tomaskovacik/vwcdavr/dumps/dump_cdc_real_changer_real_radio_audi_concert1.txt

0 CF FF FF 5A 5F FF FF                  CD: 70 track: 0   min: 0 sek: A5
FF FF C7 DE 5A 17 0 7F                  CD: 40 track: 38   min: 21 sek: A5
FF FF FF DE 5A 5F FF FF                  CD: 40 track: 0   min: 21 sek: A5
FF FB 42 D0 F FF FF BC                  CD: 44 track: BD   min: 2F sek: F0
FF FF BC B4 BF FF FF FF                  CD: 40 track: 43   min: 4B sek: 40
B4 FF FF FF FF FF 8F BC                  CD: 40 track: 0   min: 0 sek: 0
FF FF FF FF 8F BC B4 2B                  CD: 40 track: 0   min: 0 sek: 70
B4 BF FF FF B4 FF FF BC                  CD: 0 track: 0   min: 0 sek: 4B
B4 2A 0 FF FF FF FF BC                  CD: 95 track: FF   min: 0 sek: 0
B4 29 0 FF FF FF FF BF                  CD: 96 track: FF   min: 0 sek: 0
532C10EF - DISABLE
B4 BF FF FF FF FF 8F BC                  CD: 0 track: 0   min: 0 sek: 0
532C14EB - end cmd/next cd
D4 7F FF FF FF FF 1F B8                  CD: C0 track: 0   min: 0 sek: 0
7A 5F FF FF FF FF C7 FE                  CD: E0 track: 0   min: 0 sek: 0
F4 29 0 FF FF FF FF F4                  CD: 96 track: FF   min: 0 sek: 0
F4 FF FC FF FF FF FF FC                  CD: 40 track: 3   min: 0 sek: 0
29 0 FF FF FF FF FC F4                  CD: BF track: 0   min: 0 sek: 0
F4 BF FF FF FC FF 8F FC                  CD: 0 track: 0   min: 0 sek: 3
F4 DF FF FF FF FF C7 FE                  CD: 60 track: 0   min: 0 sek: 0
F4 BF FF FF FF FF 8F FC                  CD: 0 track: 0   min: 0 sek: 0
F4 BF FF FF FF FF 8F FE                  CD: 0 track: 0   min: 0 sek: 0
F4 BF FF FF FF FF 8F FC                  CD: 0 track: 0   min: 0 sek: 0
B4 2E 0 FF FF FF FF BC                  CD: 91 track: FF   min: 0 sek: 0
B4 BE FE FF FF FF 6F BC                  CD: 1 track: 1   min: 0 sek: 0
B4 2D 0 FF FF FF FF BC                  CD: 92 track: FF   min: 0 sek: 0
B4 BE FE FF FF FF 6F BC                  CD: 1 track: 1   min: 0 sek: 0
B4 2C 0 FF FF FF FF BC                  CD: 93 track: FF   min: 0 sek: 0
B4 7D FF B4 FF FF FF BC                  CD: C2 track: 0   min: 4B sek: 0
B4 2B 0 FF FF FF FF BC                  CD: 94 track: FF   min: 0 sek: 0
B4 2A 0 FF FF FB FE FF                  CD: 95 track: FF   min: 0 sek: 0
68 7D FD FF FF FE DF 78                  CD: C2 track: 2   min: 0 sek: 0
2D 2F BF BF FF FF DB EF                  CD: 90 track: 40   min: 40 sek: 0
B4 FF FF F7 FF FF 6F BC                  CD: 40 track: 0   min: 8 sek: 0
BE FE FF FF FF 6F BC B4                  CD: 41 track: 0   min: 0 sek: 0
B4 BE FE FF BC 0 FF BC                  CD: 1 track: 1   min: 0 sek: 43
B4 2C 0 FF FF FF FF BC                  CD: 93 track: FF   min: 0 sek: 0
B4 2B 0 FF FF FF FF B4                  CD: 94 track: FF   min: 0 sek: 0
B4 FF 79 FF FF FF FF 7C                  CD: 40 track: 86   min: 0 sek: 0
FF FF FF FF BE 5A 5F 7F                  CD: 40 track: 0   min: 0 sek: 41
B4 29 0 FF BC FF 6F BC                  CD: 96 track: FF   min: 0 sek: 43
B4 BE FE FF FF FF 6F BC                  CD: 1 track: 1   min: 0 sek: 0
B4 2D 0 FF FF FF FF BC                  CD: 92 track: FF   min: 0 sek: 0
B4 BE FE FF FF FF 6F BC                  CD: 1 track: 1   min: 0 sek: 0
B4 2C 0 FF FF FF FF BC                  CD: 93 track: FF   min: 0 sek: 0
B4 BE FF 6F 0 FF FF BC                  CD: 1 track: 0   min: 90 sek: FF
B4 2B 0 FF FF FF FF BC                  CD: 94 track: FF   min: 0 sek: 0
B4 2A 0 FF FF FF B4 FF                  CD: 95 track: FF   min: 0 sek: 0
B4 FF FF FF 6F BC FF BC                  CD: 40 track: 0   min: 0 sek: 90
FF BC B4 BE FE FF FF FF                  CD: 3 track: 4B   min: 41 sek: 1
B4 0 FF B4 FF FF 6F BC                  CD: BF track: 0   min: 4B sek: 0
B4 BE FE FF FF FF 6F BC                  CD: 1 track: 1   min: 0 sek: 0
B4 2C 0 FF FF FF FF BC                  CD: 93 track: FF   min: 0 sek: 0
B4 BE FE FF FF FF 6F BC                  CD: 1 track: 1   min: 0 sek: 0
B4 2B 0 FF FF FF FF BC                  CD: 94 track: FF   min: 0 sek: 0
B4 FF 6F A8 FF FF FF BC                  CD: 40 track: 90   min: 57 sek: 0
B4 2A 0 FF FF FF FF BC                  CD: 95 track: FF   min: 0 sek: 0
B4 29 0 FF FE BE FF BC                  CD: 96 track: FF   min: 0 sek: 1
B4 BE FE FF FF FF 6F BC                  CD: 1 track: 1   min: 0 sek: 0
B4 2D 0 FF FF FF FF BC                  CD: 92 track: FF   min: 0 sek: 0
B4 BE FE FF FF FF 6F BC                  CD: 1 track: 1   min: 0 sek: 0
B4 2C 0 FF FF FF FF BC                  CD: 93 track: FF   min: 0 sek: 0
B4 BE FE FF 6F 2B FF BC                  CD: 1 track: 1   min: 0 sek: 90
B4 2B 0 FF FF FF FF BC                  CD: 94 track: FF   min: 0 sek: 0
B4 2A 0 FF FF FF FF BC                  CD: 95 track: FF   min: 0 sek: 0
B4 FE 6F FF FF FF FF BC                  CD: 41 track: 90   min: 0 sek: 0
FF FF FF FF BC B4 BE FE                  CD: 40 track: 0   min: 0 sek: 43
B4 2E 0 FF 74 FF B7 DE                  CD: 91 track: FF   min: 0 sek: 8B
BA 5F 7F 7F FF FF B7 DE                  CD: E0 track: 80   min: 80 sek: 0
B4 BE FE FF FF BC FF FF                  CD: 1 track: 1   min: 0 sek: 0
B4 FF FF FF FF BC 6F BC                  CD: 40 track: 0   min: 0 sek: 0
6F BC B4 2B 0 FF FF FF                  CD: 3 track: 4B   min: D4 sek: FF
B4 FF 6F 2A FF FF FF BC                  CD: 40 track: 90   min: D5 sek: 0
B4 2A 0 FF FF FF FF BC                  CD: 95 track: FF   min: 0 sek: 0
B4 29 0 FF FF FE FF BC                  CD: 96 track: FF   min: 0 sek: 0
B4 BE FE FF FF FF 6F BC                  CD: 1 track: 1   min: 0 sek: 0
B4 2D 0 FF FF FF FF BC                  CD: 92 track: FF   min: 0 sek: 0
B4 BD FE FF FF FF 6F BC                  CD: 2 track: 1   min: 0 sek: 0
B4 2C 0 FF FF FF FF BC                  CD: 93 track: FF   min: 0 sek: 0
B4 BD FE FF B4 0 FF BC                  CD: 2 track: 1   min: 0 sek: 4B
B4 2B 0 FF FF FF FF BC                  CD: 94 track: FF   min: 0 sek: 0
B4 2A 0 FF FF FF FF BC                  CD: 95 track: FF   min: 0 sek: 0
B4 FF 6F FF FF FF FF BC                  CD: 40 track: 90   min: 0 sek: 0
0 FF FF FF FF BC B4 BD                  CD: 40 track: 0   min: 0 sek: 0
B4 2E EC DC B4 FF 6F BC                  CD: 91 track: 13   min: 23 sek: 4B
B4 BD FE FF FF FF 6F BC                  CD: 2 track: 1   min: 0 sek: 0
B4 2C 0 FF FF FF FF BC                  CD: 93 track: FF   min: 0 sek: 0
B4 BD FE FF FF FF 6F BC                  CD: 2 track: 1   min: 0 sek: 0
B4 2B 0 FF FF FF FF BC                  CD: 94 track: FF   min: 0 sek: 0
9A 5E FF DE 2A FF FF BC                  CD: E1 track: 0   min: 21 sek: D5
B4 2A 0 FF FF FF FF BC                  CD: 95 track: FF   min: 0 sek: 0
B4 29 0 FF FF FF FE FF                  CD: 96 track: FF   min: 0 sek: 0
B4 FF FF FF 6F BC FF BC                  CD: 40 track: 0   min: 0 sek: 90
FF BC B4 BD FE FF FF FF                  CD: 3 track: 4B   min: 42 sek: 1
B4 FF FF FE FF FF 6F BC                  CD: 40 track: 0   min: 1 sek: 0
B4 BD FE FF FF FF 6F BC                  CD: 2 track: 1   min: 0 sek: 0
B4 2B 0 FF FF FF FF BC                  CD: 94 track: FF   min: 0 sek: 0
B4 BD FE FF FF FF 6F BC                  CD: 2 track: 1   min: 0 sek: 0
B4 2A 0 FF FF FF FF BC                  CD: 95 track: FF   min: 0 sek: 0
B4 FF 6F 0 FF FF FF BC                  CD: 40 track: 90   min: FF sek: 0
29 0 FF FF FF FF BC B4                  CD: BF track: 0   min: 0 sek: 0
B4 2E EC CE FF FE FF BC                  CD: 91 track: 13   min: 31 sek: 0
B4 BD FE FF FF FF 6F BC                  CD: 2 track: 1   min: 0 sek: 0
B4 2C 0 FF FF FF FF BC                  CD: 93 track: FF   min: 0 sek: 0
B4 BD FE FF FF FF 6F BC                  CD: 2 track: 1   min: 0 sek: 0
B4 2B 0 FF FF FF FF DE                  CD: 94 track: FF   min: 0 sek: 0
B4 BD FE B7 2A FF FF BC                  CD: 2 track: 1   min: 48 sek: D5
B4 2A 0 FF FF FF FF BC                  CD: 95 track: FF   min: 0 sek: 0
B4 29 0 7F FF FF DE FF                  CD: 96 track: FF   min: 80 sek: 0
B4 FF FB 7D ED DC FF BC                  CD: 40 track: 4   min: 82 sek: 12
DD CF FB CB 4B CF EF FF                  CD: 70 track: 4   min: 34 sek: B4
B4 FF FF BC FF FF 6F BC                  CD: 40 track: 0   min: 43 sek: 0
B4 BC FE FF FF FF 6F BC                  CD: 3 track: 1   min: 0 sek: 0
B4 2B 80 7F FF FF FF DE                  CD: 94 track: 7F   min: 80 sek: 0
B4 BC FE FF FF FF 6F BC                  CD: 3 track: 1   min: 0 sek: 0
B4 2A 0 FF FF FF FF B4                  CD: 95 track: FF   min: 0 sek: 0
B4 FF 6F BC FF FF FF BC                  CD: 40 track: 90   min: 43 sek: 0
FF FF FF BC B4 BC FE FF                  CD: 40 track: 0   min: 43 sek: 4B
B4 67 FF BC FF FF 6F BC                  CD: D8 track: 0   min: 43 sek: 0
B4 BC FE FF FF FF 6F BC                  CD: 3 track: 1   min: 0 sek: 0
B4 2C 0 FF FF FF FF BC                  CD: 93 track: FF   min: 0 sek: 0
B4 BC FE FF FF FF 6F BC                  CD: 3 track: 1   min: 0 sek: 0
B4 2B 0 7F FF FF FF DE                  CD: 94 track: FF   min: 80 sek: 0
B4 FF DF A8 FF FF FF EF                  CD: 40 track: 20   min: 57 sek: 0
B4 2A 0 7F FF FF FF EF                  CD: 95 track: FF   min: 80 sek: 0
B4 29 0 FF BC FE FF BC                  CD: 96 track: FF   min: 0 sek: 43
B4 BC FE FF FF FF 6F BC                  CD: 3 track: 1   min: 0 sek: 0
B4 DA 0 FF FF FF FF BC                  CD: 65 track: FF   min: 0 sek: 0
5A BC FE FF FF FF 6F BC                  CD: 3 track: 1   min: 0 sek: 0
5A B 0 3F FF FF FF F7                  CD: B4 track: FF   min: C0 sek: 0
B4 BC FE FF 15 FF FF BC                  CD: 3 track: 1   min: 0 sek: EA
B4 2B 0 FF FF FF FF BC                  CD: 94 track: FF   min: 0 sek: 0
B4 2A 0 FF FF FF FF BC                  CD: 95 track: FF   min: 0 sek: 0
B4 FF DE FF FF FF FF BC                  CD: 40 track: 21   min: 0 sek: 0
FF FF FF FF BC B4 BC FE                  CD: 40 track: 0   min: 0 sek: 43
B4 CE FF BC FF FF 6F BC                  CD: 71 track: 0   min: 43 sek: 0
B4 BC FE FF FF FF 6F BC                  CD: 3 track: 1   min: 0 sek: 0
B4 2C 0 FF FF FF FF BC                  CD: 93 track: FF   min: 0 sek: 0
B4 BC FE FF FF FF 6F BC                  CD: 3 track: 1   min: 0 sek: 0
B4 2B 0 FF FF FF FF BC                  CD: 94 track: FF   min: 0 sek: 0
B4 FF 6F 1 FF FF FF DE                  CD: 40 track: 90   min: FE sek: 0
B4 2A 0 FF FF FF FF DE                  CD: 95 track: FF   min: 0 sek: 0
B4 29 0 FF FF BC FF 6F                  CD: 96 track: FF   min: 0 sek: 0
B4 BC FE FF FF FF 6F BC                  CD: 3 track: 1   min: 0 sek: 0
B4 6D 0 FF FF FF FF DE                  CD: D2 track: FF   min: 0 sek: 0
B4 BC FE FF FF FF 6F BC                  CD: 3 track: 1   min: 0 sek: 0
B4 2C 0 FF FF FF FF BC                  CD: 93 track: FF   min: 0 sek: 0
B4 BC FE FF 6F 2B FF BC                  CD: 3 track: 1   min: 0 sek: 90
B4 2B 0 FF FF FF FF BC                  CD: 94 track: FF   min: 0 sek: 0
B4 2A 0 FF FF FF FF BC                  CD: 95 track: FF   min: 0 sek: 0
B4 FE 6F FF FF FF FF BC                  CD: 41 track: 90   min: 0 sek: 0
0 FF FF FF FF BC B4 BC                  CD: 40 track: 0   min: 0 sek: 0
B4 2E EC CE FF BC FF BC                  CD: 91 track: 13   min: 31 sek: 0
B4 BC FE FF FF FF 6F BC                  CD: 3 track: 1   min: 0 sek: 0
B4 2C 0 FF FF FF FF BC                  CD: 93 track: FF   min: 0 sek: 0
B4 BC FE FF FF FF 6F BC                  CD: 3 track: 1   min: 0 sek: 0
B4 2B 0 FF FF FF FF BC                  CD: 94 track: FF   min: 0 sek: 0
B4 BC FE 6F 2A FF FF BC                  CD: 3 track: 1   min: 90 sek: D5
B4 2A 0 FF FF FF FF BC                  CD: 95 track: FF   min: 0 sek: 0
B4 29 0 FF FF FF FF FE                  CD: 96 track: FF   min: 0 sek: 0
B4 FF 6F BC AD DC FF BC                  CD: 40 track: 90   min: 43 sek: 52
AD DC FF BC B4 BC FE FF                  CD: 63 track: 0   min: 43 sek: 4B
B4 FF FF FE FF FF 6F BC                  CD: 40 track: 0   min: 1 sek: 0
BC FE FF FF FF 6F BC B4                  CD: 41 track: 0   min: 0 sek: 0
B4 BC FE FF 6F 0 FF BC                  CD: 3 track: 1   min: 0 sek: 90
B4 2B 0 FF FF FF FF BC                  CD: 94 track: FF   min: 0 sek: 0
B4 2A 0 FF FF FF FF B4                  CD: 95 track: FF   min: 0 sek: 0
B4 FF 6F FF FF FF FF BC                  CD: 40 track: 90   min: 0 sek: 0
29 0 FF FF FF FF BC B4                  CD: BF track: 0   min: 0 sek: 0
B4 2E EC CE FF BC FF DE                  CD: 91 track: 13   min: 31 sek: 0
B4 BC FE FF FF FF 6F DE                  CD: 3 track: 1   min: 0 sek: 0
B4 BC FE FF FF FF F7 2C                  CD: 3 track: 1   min: 0 sek: 0
B4 FF FF FF FF FF 6F BC                  CD: 40 track: 0   min: 0 sek: 0
FF FF FF 6F BC B4 2B 0                  CD: 40 track: 0   min: 90 sek: 43
B4 BC FF 6F 0 FF FF BC                  CD: 3 track: 0   min: 90 sek: FF
B4 2A 0 FF FF FF FF BC                  CD: 95 track: FF   min: 0 sek: 0
B4 29 0 FF FF FF B4 FE                  CD: 96 track: FF   min: 0 sek: 0
B4 FF EE FB CD DC FF BC                  CD: 40 track: 11   min: 4 sek: 32
6E E7 FD E5 A5 E7 F7 FF                  CD: 58 track: 2   min: 1A sek: 5A
B4 FF BC FE FF FF 6F BC                  CD: 40 track: 43   min: 1 sek: 0
BC FE FF FF FF 6F BC B4                  CD: 41 track: 0   min: 0 sek: 0
B4 BC 7F FF DE FF FF BC                  CD: 3 track: 80   min: 0 sek: 21
B4 2B 0 FF FF FF FF BC                  CD: 94 track: FF   min: 0 sek: 0
B4 2A 0 FF FF FF FF B4                  CD: 95 track: FF   min: 0 sek: 0
B4 FE 6F BC FF FF FF BC                  CD: 41 track: 90   min: 43 sek: 0
FF FF FF BC B4 BB FE FF                  CD: 40 track: 0   min: 43 sek: 4B
B4 EC AD B4 FF FF 6F BC                  CD: 53 track: 52   min: 4B sek: 0
B4 BB FE FF FF FF 6F BC                  CD: 4 track: 1   min: 0 sek: 0
B4 BB FE FF 6F 2C 8E BC                  CD: 4 track: 1   min: 0 sek: 90
B4 2C E8 8E 98 CE FF BC                  CD: 93 track: 17   min: 71 sek: 67
B4 2B 0 FF FF FF FF FF                  CD: 94 track: FF   min: 0 sek: 0
B4 FF BC FF FF FF FF BC                  CD: 40 track: 43   min: 0 sek: 0
FF FF FF FF BC B4 BB FE                  CD: 40 track: 0   min: 0 sek: 43
B4 29 FF EF 77 FF B7 DE                  CD: 96 track: 0   min: 10 sek: 88
B4 BB FF 7F FF FF B7 DE                  CD: 4 track: 0   min: 80 sek: 0
B4 BB FE FF ED C1 FF EF                  CD: 4 track: 1   min: 0 sek: 12
B0 6D 0 FF FF FF FF BC                  CD: D2 track: FF   min: 0 sek: 0
B4 2C E8 8E 98 CE FF BC                  CD: 93 track: 17   min: 71 sek: 67
B4 FF BE FF FF FF FF BC                  CD: 40 track: 41   min: 0 sek: 0
0 FF FF FF FF BC B4 BB                  CD: 40 track: 0   min: 0 sek: 0
B4 2A 0 FF B4 FF 6F BC                  CD: 95 track: FF   min: 0 sek: 4B
B4 BB FE FF FF FF 6F BC                  CD: 4 track: 1   min: 0 sek: 0
B4 2E EC CE AD DC FF BC                  CD: 91 track: 13   min: 31 sek: 52
B4 BB FE FF FF FF 6F 9E                  CD: 4 track: 1   min: 0 sek: 0
B4 6D 0 FF FF FF FF BC                  CD: D2 track: FF   min: 0 sek: 0
B4 BF FF B4 8E CE FF BC                  CD: 0 track: 0   min: 4B sek: 71
B4 2C E8 8E 98 CE FF BC                  CD: 93 track: 17   min: 71 sek: 67
B4 2B 0 FF BC FF 6F BC                  CD: 94 track: FF   min: 0 sek: 43
B4 BB FE FF FF FF 6F BC                  CD: 4 track: 1   min: 0 sek: 0
5A 5D FF 7F FF FF B7 B4                  CD: E2 track: 0   min: 80 sek: 0
B4 FF FF BC FF FF 6F BC                  CD: 40 track: 0   min: 43 sek: 0
FF FF 6F BC B4 2E EC CE                  CD: 40 track: 90   min: 43 sek: 4B
B4 FE 6F B4 FF FF FF BC                  CD: 41 track: 90   min: 4B sek: 0
B4 6D 0 FF FF FF FF BC                  CD: D2 track: FF   min: 0 sek: 0
B4 2C E8 8E CE BB FF BC                  CD: 93 track: 17   min: 71 sek: 31
B4 BB FE FF FF FF 6F BC                  CD: 4 track: 1   min: 0 sek: 0
B4 2A 0 FF FF FF FF BC                  CD: 95 track: FF   min: 0 sek: 0
B4 BB FE FF FF FF 6F BC                  CD: 4 track: 1   min: 0 sek: 0
B4 29 0 FF FF FF FF DE                  CD: 96 track: FF   min: 0 sek: 0
B6 5D FF FB EC DC 7F DE                  CD: E2 track: 0   min: 4 sek: 13
B4 2E EC CE AD DC 7F DE                  CD: 91 track: 13   min: 31 sek: 52
B4 6D 0 FF FF BC F7 6F                  CD: D2 track: FF   min: 0 sek: 0
B4 BB FE FF FF FF 6F BC                  CD: 4 track: 1   min: 0 sek: 0
B4 BB FE 7F FF FF B7 DE                  CD: 4 track: 1   min: 80 sek: 0
B4 0 FF BB FF FF 6F BC                  CD: BF track: 0   min: 44 sek: 0
B4 BB FE FF FF FF 6F BC                  CD: 4 track: 1   min: 0 sek: 0
B4 29 0 FF FF FF FF BC                  CD: 96 track: FF   min: 0 sek: 0
B4 BB FE FF FF FF 6F BC                  CD: 4 track: 1   min: 0 sek: 0
B4 2E EC CE AD DC FF BC                  CD: 91 track: 13   min: 31 sek: 52
5A 7F B7 0 FF FF FF BC                  CD: C0 track: 48   min: FF sek: 0
6D 0 FF FF FF FF BC B4                  CD: BF track: 0   min: 0 sek: 0
B4 2C E8 98 BC FE 6F BC                  CD: 93 track: 17   min: 67 sek: 43
B4 BB FE FF FF FF 6F BC                  CD: 4 track: 1   min: 0 sek: 0
B4 2A 0 FF FF FF FF BC                  CD: 95 track: FF   min: 0 sek: 0
B4 BB FE FF FF FF 6F BC                  CD: 4 track: 1   min: 0 sek: 0
B4 29 0 FF FF FF FF BC                  CD: 96 track: FF   min: 0 sek: 0
B4 BB FF FF 2E AD FF BC                  CD: 4 track: 0   min: 0 sek: D1
B4 2E EC CE AD DC FF BC                  CD: 91 track: 13   min: 31 sek: 52
B4 6D 0 FF FF BC FE FF                  CD: D2 track: FF   min: 0 sek: 0
B4 FD FF FF FE DF BD 78                  CD: 42 track: 0   min: 0 sek: 1
BC 5A 5D FF 7F FF FF B7                  CD: E5 track: A2   min: 0 sek: 80
B4 FF BC FE FF FF 6F BC                  CD: 40 track: 43   min: 1 sek: 0
B4 BB FE FF FF FF 6F BC                  CD: 4 track: 1   min: 0 sek: 0
B4 29 0 FF FF FF FF BC                  CD: 96 track: FF   min: 0 sek: 0
B4 BB FE FF FF FF 6F BC                  CD: 4 track: 1   min: 0 sek: 0
B4 2E EC CE AD DC FF B4                  CD: 91 track: 13   min: 31 sek: 52
B4 FF 6F BC FF FF FF BC                  CD: 40 track: 90   min: 43 sek: 0
FF FF FF BC B4 BB FE FF                  CD: 40 track: 0   min: 43 sek: 4B
B4 8E CE BB FF FF 6F BC                  CD: 31 track: 31   min: 44 sek: 0
B4 BB FE FF FF FF 6F BC                  CD: 4 track: 1   min: 0 sek: 0
B4 2A 0 FF FF FF FF BC                  CD: 95 track: FF   min: 0 sek: 0
B6 5D FF 7F FF FF B7 DE                  CD: E2 track: 0   min: 80 sek: 0
B4 29 0 FF FF FF FF B4                  CD: 96 track: FF   min: 0 sek: 0
B4 FF DE CE AD DC FF BC                  CD: 40 track: 21   min: 31 sek: 52
D9 9D 5B B9 FF 79 69 77                  CD: 22 track: A4   min: 46 sek: 0
B4 0 FF BC FF FF 6F BC                  CD: BF track: 0   min: 43 sek: 0
B4 BB FE FF FF FF 6F BC                  CD: 4 track: 1   min: 0 sek: 0
B4 2B E6 6E 87 D7 FF BC                  CD: 94 track: 19   min: 91 sek: 78
B4 BB FE FF FF FF 6F BC                  CD: 4 track: 1   min: 0 sek: 0
B4 2A 0 FF FF FF FF BC                  CD: 95 track: FF   min: 0 sek: 0
B4 FE 6F FF FF FF FF BC                  CD: 41 track: 90   min: 0 sek: 0
29 0 FF FF FF FF BC B4                  CD: BF track: 0   min: 0 sek: 0
B4 2E EC D5 BC FE FF BC                  CD: 91 track: 13   min: 2A sek: 43
B4 BB FE FF FF FF 6F BC                  CD: 4 track: 1   min: 0 sek: 0
B4 2C E8 8E 98 CF 7F DE                  CD: 93 track: 17   min: 71 sek: 67
B4 BA FE FF FF FF 6F BC                  CD: 5 track: 1   min: 0 sek: 0
B4 2B E6 6E 87 D7 FF BC                  CD: 94 track: 19   min: 91 sek: 78
B4 FF 6F 2A FF FF FF BC                  CD: 40 track: 90   min: D5 sek: 0
B4 2A 0 FF FF FF FF BC                  CD: 95 track: FF   min: 0 sek: 0
B4 29 0 FF BC FE FF BC                  CD: 96 track: FF   min: 0 sek: 43
B4 BA FE FF FF FF 6F BC                  CD: 5 track: 1   min: 0 sek: 0
B4 6D 0 FF FF FF FF BC                  CD: D2 track: FF   min: 0 sek: 0
B4 BA FE FF FF FF 6F BC                  CD: 5 track: 1   min: 0 sek: 0
B4 2C E8 8E 98 CE FF BC                  CD: 93 track: 17   min: 71 sek: 67
B4 BA FF BC 57 7 FF DE                  CD: 5 track: 0   min: 43 sek: A8
B4 2B E6 6E 83 EB FF DE                  CD: 94 track: 19   min: 91 sek: 7C
B4 2A 0 FF FF FF FE FF                  CD: 95 track: FF   min: 0 sek: 0
B4 BA FE FF FF FF 6F BC                  CD: 5 track: 1   min: 0 sek: 0
B4 2E EC CE AD DC FF BC                  CD: 91 track: 13   min: 31 sek: 52
B4 BA FE FF FF FF 6F BC                  CD: 5 track: 1   min: 0 sek: 0
B4 36 80 7F FF FF FF DE                  CD: 89 track: 7F   min: 80 sek: 0
B4 BA FE FF 2C 98 FF BC                  CD: 5 track: 1   min: 0 sek: D3
B4 2C E8 8E 98 CE FF BC                  CD: 93 track: 17   min: 71 sek: 67
B4 2B E6 6E 87 FF FE FF                  CD: 94 track: 19   min: 91 sek: 78
B4 BA FE FF FF FF 6F BC                  CD: 5 track: 1   min: 0 sek: 0
B4 29 0 FF FF FF FF BC                  CD: 96 track: FF   min: 0 sek: 0
B4 BA FE FF FF FF 6F BC                  CD: 5 track: 1   min: 0 sek: 0
B4 2E EC CE AD DC FF BC                  CD: 91 track: 13   min: 31 sek: 52
B4 BA FE FF BC 0 FF BC                  CD: 5 track: 1   min: 0 sek: 43
B4 6D 0 FF FF FF FF BC                  CD: D2 track: FF   min: 0 sek: 0
B4 2C E8 8E 98 CE BC BA                  CD: 93 track: 17   min: 71 sek: 67
B4 FF FF 6F BC D7 FF BC                  CD: 40 track: 0   min: 90 sek: 43
D7 FF BC B4 BA FE FF FF                  CD: 40 track: 43   min: 4B sek: 45
B4 FF BC FE FF FF 6F BC                  CD: 40 track: 43   min: 1 sek: 0
BA FE FF FF FF 6F BC B4                  CD: 41 track: 0   min: 0 sek: 0
B4 BA FE FF B4 75 FF BC                  CD: 5 track: 1   min: 0 sek: 4B
B4 2E EC CE AD DC FF BC                  CD: 91 track: 13   min: 31 sek: 52
B4 6D 0 FF FF FF BA FF                  CD: D2 track: FF   min: 0 sek: 0
B4 FF FF FF 6F BC FF BC                  CD: 40 track: 0   min: 0 sek: 90
FF BC B4 BA FE FF FF FF                  CD: 3 track: 4B   min: 45 sek: 1
B4 E6 FF BA FF FF 6F BC                  CD: 59 track: 0   min: 45 sek: 0
B4 BA FE FF FF FF 6F BC                  CD: 5 track: 1   min: 0 sek: 0
B4 29 0 FF FF FF FF BC                  CD: 96 track: FF   min: 0 sek: 0
B4 BA FE FF FF FF 6F BC                  CD: 5 track: 1   min: 0 sek: 0
B4 2E EC CE AD DC FF B4                  CD: 91 track: 13   min: 31 sek: 52
B4 FF 6F BC FF FF FF BC                  CD: 40 track: 90   min: 43 sek: 0
FF FF FF BC B4 BA FE FF                  CD: 40 track: 0   min: 43 sek: 4B
B4 E8 DF FE FF FF 6F BC                  CD: 57 track: 20   min: 1 sek: 0
B4 BA FE FF FF FF 6F BC                  CD: 5 track: 1   min: 0 sek: 0
B4 2A 0 FF FF FF FF BC                  CD: 95 track: FF   min: 0 sek: 0
B4 BA FE FF FF FF 6F BC                  CD: 5 track: 1   min: 0 sek: 0
B4 29 0 FF FF FF FF BC                  CD: 96 track: FF   min: 0 sek: 0
B4 FF FF 2E AD DC FF BC                  CD: 40 track: 0   min: D1 sek: 52
B4 2E EC CE AD DC FF BC                  CD: 91 track: 13   min: 31 sek: 52
B4 6D 0 FF BA FF 6F BC                  CD: D2 track: FF   min: 0 sek: 45
B4 BA FE FF FF FF 6F BC                  CD: 5 track: 1   min: 0 sek: 0
B4 2B E6 6E 87 D7 FF BC                  CD: 94 track: 19   min: 91 sek: 78
B4 BA FE FF FF FF 6F BC                  CD: 5 track: 1   min: 0 sek: 0
B4 2A 0 FF FF FF FF BC                  CD: 95 track: FF   min: 0 sek: 0
B4 FE 6F B4 FF FF FF BC                  CD: 41 track: 90   min: 4B sek: 0
B4 29 0 FF FF FF FF BC                  CD: 96 track: FF   min: 0 sek: 0
B4 2E EC CE FF FE FF BC                  CD: 91 track: 13   min: 31 sek: 0
B4 BA FE FF FF FF 6F BC                  CD: 5 track: 1   min: 0 sek: 0
9A 5D 7F 7F FF FF B7 B4                  CD: E2 track: 80   min: 80 sek: 0
B4 98 BC FF FF FF 6F BC                  CD: 27 track: 43   min: 0 sek: 0
FF FF FF 6F BC B4 2B E6                  CD: 40 track: 0   min: 90 sek: 43
B4 FE FF B4 FF FF FF BC                  CD: 41 track: 0   min: 4B sek: 0
B4 2A 0 FF FF FF FF BC                  CD: 95 track: FF   min: 0 sek: 0
B4 29 0 FF FF BC FE 6F                  CD: 96 track: FF   min: 0 sek: 0
B4 BA FE FF FF FF 6F BC                  CD: 5 track: 1   min: 0 sek: 0
B4 6D 0 FF FF FF FF BC                  CD: D2 track: FF   min: 0 sek: 0
B4 BA FE FF FF FF 6F BC                  CD: 5 track: 1   min: 0 sek: 0
B4 2C E8 8E 98 CE FF BC                  CD: 93 track: 17   min: 71 sek: 67
B4 BA FE FF BC 6E FF BC                  CD: 5 track: 1   min: 0 sek: 43
B4 2B E6 6E 87 D7 FF BC                  CD: 94 track: 19   min: 91 sek: 78
B4 2A 0 FF FF FF B4 FF                  CD: 95 track: FF   min: 0 sek: 0
B4 FF FF ED F7 9F FF BC                  CD: 40 track: 0   min: 12 sek: 8
FF FD E5 A5 D7 F7 FF FF                  CD: 42 track: 1A   min: 5A sek: 28
B4 EA BC FF FF FF 6F BC                  CD: 55 track: 43   min: 0 sek: 0
BA FE FF FF FF 6F BC B4                  CD: 41 track: 0   min: 0 sek: 0
B4 BA FE FF BC E8 CE BC                  CD: 5 track: 1   min: 0 sek: 43
B4 2C E8 8E 98 CE FF BC                  CD: 93 track: 17   min: 71 sek: 67
B4 2B E6 6E 87 FF BA FF                  CD: 94 track: 19   min: 91 sek: 78
B6 5D 7F 7F FF FF B7 DE                  CD: E2 track: 80   min: 80 sek: 0
B4 BA FE FF FF FF 6F B4                  CD: 5 track: 1   min: 0 sek: 0
B4 FF BC FE FF FF 6F BC                  CD: 40 track: 43   min: 1 sek: 0
B4 B9 FE FF FF FF 6F BC                  CD: 6 track: 1   min: 0 sek: 0
B4 6D 0 FF FF FF FF BC                  CD: D2 track: FF   min: 0 sek: 0
B4 B9 FE FF FF FF 6F BC                  CD: 6 track: 1   min: 0 sek: 0
B4 2C E8 8E 98 CE FF BC                  CD: 93 track: 17   min: 71 sek: 67
B4 FD 6F 6E 87 D7 FF BC                  CD: 42 track: 90   min: 91 sek: 78
6E 87 D7 FF BC B4 B9 FE                  CD: 38 track: 28   min: 0 sek: 43
B4 AE EF B9 FF FF 6F BC                  CD: 11 track: 10   min: 46 sek: 0
B4 B9 FE FF FF FF 6F BC                  CD: 6 track: 1   min: 0 sek: 0
B4 2E EC CE AD DC FF BC                  CD: 91 track: 13   min: 31 sek: 52
B4 B9 FE FF FF FF 6F BC                  CD: 6 track: 1   min: 0 sek: 0
B4 6D 0 FF FF FF BC B9                  CD: D2 track: FF   min: 0 sek: 0
B4 EF DF 7D 38 CE FF BC                  CD: 50 track: 20   min: 82 sek: C7
9C 67 7F DE 5A 5C FF 7F                  CD: D8 track: 80   min: 21 sek: A5
B4 6E BC B9 FF FF 6F BC                  CD: D1 track: 43   min: 46 sek: 0
B4 B9 FE FF FF FF 6F BC                  CD: 6 track: 1   min: 0 sek: 0
B4 B9 FE FF 9E 0 FF BC                  CD: 6 track: 1   min: 0 sek: 61
B4 29 0 FF FF FF FF BC                  CD: 96 track: FF   min: 0 sek: 0
B4 2E EC CE AD DC FF B9                  CD: 91 track: 13   min: 31 sek: 52
B4 FF DF 79 FF FF FF BC                  CD: 40 track: 20   min: 86 sek: 0
FF FF FF DE 5A 5C FF 7F                  CD: 40 track: 0   min: 21 sek: A5
B4 8E FF B9 FF FF 6F BC                  CD: 31 track: 0   min: 46 sek: 0
B4 B9 FE FF FF FF 6F BC                  CD: 6 track: 1   min: 0 sek: 0
B4 2A EA AE 9A DA FF BC                  CD: 95 track: 15   min: 51 sek: 65
B4 B9 FE FF FF FF 6F BC                  CD: 6 track: 1   min: 0 sek: 0
B4 29 0 FF FF FF FF B9                  CD: 96 track: FF   min: 0 sek: 0
B4 FF BC CE AD DC FF BC                  CD: 40 track: 43   min: 31 sek: 52
EC CE AD DC FF BC B4 B9                  CD: 71 track: 52   min: 23 sek: 0
B4 0 FF BC FF FF 6F BC                  CD: BF track: 0   min: 43 sek: 0
B4 B9 FE FF FF FF 6F BC                  CD: 6 track: 1   min: 0 sek: 0
B4 2B E6 6E 87 D7 FF BC                  CD: 94 track: 19   min: 91 sek: 78
B4 B9 FE FF FF FF 6F BC                  CD: 6 track: 1   min: 0 sek: 0
B4 2A EA AE 9A DD 7F B4                  CD: 95 track: 15   min: 51 sek: 65
B4 FF E0 FF FF FF FF BC                  CD: 40 track: 1F   min: 0 sek: 0
1F FF FF FF F7 96 97 3F                  CD: 40 track: 0   min: 0 sek: 8
B4 2E AD BC FE FF 6F BC                  CD: 91 track: 52   min: 43 sek: 1
B4 B9 FE FF FF FF 6F BC                  CD: 6 track: 1   min: 0 sek: 0
B4 B9 FE FF FF 2C 98 BC                  CD: 6 track: 1   min: 0 sek: 0
B4 E8 8E 98 CE FF BC BC                  CD: 57 track: 71   min: 67 sek: 31
BC B4 2B E6 6E 87 D7 B9                  CD: B track: D4   min: 19 sek: 91
B4 FF 78 AE 9A DA FF BC                  CD: 40 track: 87   min: 51 sek: 65
57 4D 6D 7F DE 5A 5C FF                  CD: F2 track: 92   min: 80 sek: 21
B4 0 FF B4 FF FF 6F BC                  CD: BF track: 0   min: 4B sek: 0
B4 B9 FE FF FF FF 6F BC                  CD: 6 track: 1   min: 0 sek: 0
B4 6D 0 FF FF FF FF BC                  CD: D2 track: FF   min: 0 sek: 0
B4 B9 FE FF FF FF 6F BC                  CD: 6 track: 1   min: 0 sek: 0
B4 2C E8 8E 98 CE FF BC                  CD: 93 track: 17   min: 71 sek: 67
B4 FF 6F 6E 87 D7 FF BC                  CD: 40 track: 90   min: 91 sek: 78
E6 6E 87 D7 FF BC B4 B9                  CD: D1 track: 78   min: 28 sek: 0
B4 2A 9A BC FE FF 6F BC                  CD: 95 track: 65   min: 43 sek: 1
B4 B9 FE FF FF FF 6F BC                  CD: 6 track: 1   min: 0 sek: 0
B4 2E EC CE AD DC FF BC                  CD: 91 track: 13   min: 31 sek: 52
B4 B9 FE FF FF FF 6F BC                  CD: 6 track: 1   min: 0 sek: 0
B4 6D 0 FF FF FF FF B4                  CD: D2 track: FF   min: 0 sek: 0
B4 FF BC 8E 98 CE FF BC                  CD: 40 track: 43   min: 71 sek: 67
E8 8E 98 CE FF BC B4 B9                  CD: 31 track: 67   min: 31 sek: 0
B4 2B F 79 FE FF B7 DE                  CD: 94 track: F0   min: 86 sek: 1
B4 BC FF 7F FF FF B7 DE                  CD: 3 track: 0   min: 80 sek: 0
B4 B9 FE FF FF BC 0 FF                  CD: 6 track: 1   min: 0 sek: 0
B4 FF FF FF FF BC 6F BC                  CD: 40 track: 0   min: 0 sek: 0
6F BC B4 2E EC CE AD DC                  CD: 3 track: 4B   min: D1 sek: 13
B4 FE 6F 3 FF FF FF BC                  CD: 41 track: 90   min: FC sek: 0
6D 0 FF FF FF FF BC B4                  CD: BF track: 0   min: 0 sek: 0
B4 2C E8 8E BC FE FF BC                  CD: 93 track: 17   min: 71 sek: 43
B4 B9 FE FF FF FF 6F BC                  CD: 6 track: 1   min: 0 sek: 0
B4 2A EA AE 9B 6D 7F DE                  CD: 95 track: 15   min: 51 sek: 64
B4 B9 FE FF FF FF 6F BC                  CD: 6 track: 1   min: 0 sek: 0
B4 29 0 FF FF FF FF BC                  CD: 96 track: FF   min: 0 sek: 0
B4 B9 FF FB EC DC FF BC                  CD: 6 track: 0   min: 4 sek: 13
B4 2E EC CE AD DC FF BC                  CD: 91 track: 13   min: 31 sek: 52
B4 6D 0 FF FF 69 FF 6F                  CD: D2 track: FF   min: 0 sek: 0
B4 B8 FF 7F FF FF B7 DE                  CD: 7 track: 0   min: 80 sek: 0
B4 B9 FE FF FF FF 6F 2D                  CD: 6 track: 1   min: 0 sek: 0
B4 6E FF FE FF FF 6F BC                  CD: D1 track: 0   min: 1 sek: 0
B4 B9 FE FF FF FF 6F BC                  CD: 6 track: 1   min: 0 sek: 0
B4 29 E8 8E 86 CF FF BC                  CD: 96 track: 17   min: 71 sek: 79
B4 B9 FE FF FF FF 6F BC                  CD: 6 track: 1   min: 0 sek: 0
B4 2E EC CE AD DC FF FE                  CD: 91 track: 13   min: 31 sek: 52
B4 FF FB 7D E7 FF FF BC                  CD: 40 track: 4   min: 82 sek: 18
FF FF F7 96 97 3F DF FF                  CD: 40 track: 8   min: 69 sek: 68
B4 8E FF B9 FF FF 6F BC                  CD: 31 track: 0   min: 46 sek: 0
B4 B9 FE FF FF FF 6F BC                  CD: 6 track: 1   min: 0 sek: 0
B4 BE FE FF 6F 85 9A BC                  CD: 1 track: 1   min: 0 sek: 90
B4 2A EA AE 9A DA FF BC                  CD: 95 track: 15   min: 51 sek: 65
B4 29 E8 8E 86 CF BC FE                  CD: 96 track: 17   min: 71 sek: 79
B4 FF FF 6F BC DC FF BC                  CD: 40 track: 0   min: 90 sek: 43
DC FF BC B4 BE FE FF FF                  CD: 40 track: 43   min: 4B sek: 41
B4 FF FF FF FF FF 6F BC                  CD: 40 track: 0   min: 0 sek: 0
FE FF FF FF 6F BC B4 2C                  CD: 40 track: 0   min: 0 sek: 90
B4 BE FF 6F E6 87 FF BC                  CD: 1 track: 0   min: 90 sek: 19
B4 2B E6 6E 87 D7 FF BC                  CD: 94 track: 19   min: 91 sek: 78
B4 2A EA AE 9A BC FE B7                  CD: 95 track: 15   min: 51 sek: 65
B4 BE FE FF FF FF 6F BC                  CD: 1 track: 1   min: 0 sek: 0
B4 2E EC CE AD DC FF BC                  CD: 91 track: 13   min: 31 sek: 52
B4 BE FE FF FF FF 6F DE                  CD: 1 track: 1   min: 0 sek: 0
B4 6D 0 FF FF FF FF BC                  CD: D2 track: FF   min: 0 sek: 0
B4 BE FE FF B4 8E FF BC                  CD: 1 track: 1   min: 0 sek: 4B
B4 2C E8 8E 98 CE FF BC                  CD: 93 track: 17   min: 71 sek: 67
B4 2B E3 37 EB B4 FF 6F                  CD: 94 track: 1C   min: C8 sek: 14
B4 BE FE FF FF FF 6F BC                  CD: 1 track: 1   min: 0 sek: 0
B4 29 E8 8E 86 CF FF BC                  CD: 96 track: 17   min: 71 sek: 79
B4 BE FE FF FF FF 6F BC                  CD: 1 track: 1   min: 0 sek: 0
B4 2E EC CE AD DC FF BC                  CD: 91 track: 13   min: 31 sek: 52
B4 BE FF BC 0 FF FF DE                  CD: 1 track: 0   min: 43 sek: FF
B4 6D 0 FF FF FF FF DE                  CD: D2 track: FF   min: 0 sek: 0
B4 2C E8 8E 98 FE BE FF                  CD: 93 track: 17   min: 71 sek: 67
B4 BE FE FF FF FF 6F BC                  CD: 1 track: 1   min: 0 sek: 0
B4 2A EA AE 9A DA FF BC                  CD: 95 track: 15   min: 51 sek: 65
B4 BE FE FF FF FF 6F BC                  CD: 1 track: 1   min: 0 sek: 0
B4 29 E8 8E 43 67 FF DE                  CD: 96 track: 17   min: 71 sek: BC
B4 BE FF 79 DC EE 7F DE                  CD: 1 track: 0   min: 86 sek: 23
B4 2E EE 67 56 EE 7F DE                  CD: 91 track: 11   min: 98 sek: A9
B4 6D 0 FF FF BE FF BC                  CD: D2 track: FF   min: 0 sek: 0
B4 BE FE FF FF FF 6F BC                  CD: 1 track: 1   min: 0 sek: 0
B4 2B E6 6E 87 D7 FF BC                  CD: 94 track: 19   min: 91 sek: 78
DA BE FE FF FF FF 6F BC                  CD: 1 track: 1   min: 0 sek: 0
5A 15 75 57 4D 6D 7F DE                  CD: AA track: 8A   min: A8 sek: B2
BA 5F 7F F7 29 CF FF BC                  CD: E0 track: 80   min: 8 sek: D6
B4 29 E8 8E 86 CF FF BC                  CD: 96 track: 17   min: 71 sek: 79
B4 2E EC CE FF BF FF BC                  CD: 91 track: 13   min: 31 sek: 0
B4 BE FE FF FF FF 6F BC                  CD: 1 track: 1   min: 0 sek: 0
B4 5F BF BF FF FF DB B4                  CD: E0 track: 40   min: 40 sek: 0
B4 8E FF FF FF FF 6F BC                  CD: 31 track: 0   min: 0 sek: 0
FF FF FF 6F BC B4 2B E6                  CD: 40 track: 0   min: 90 sek: 43
B4 BE FF BC EA DA FF BC                  CD: 1 track: 0   min: 43 sek: 15
B4 2A EA AE 9A DA FF BC                  CD: 95 track: 15   min: 51 sek: 65
B4 29 E8 8E FF FE FF BC                  CD: 96 track: 17   min: 71 sek: 0
B4 BE FE FF FF FF 6F BC                  CD: 1 track: 1   min: 0 sek: 0
B4 BE FE FF FF FF DE 6D                  CD: 1 track: 1   min: 0 sek: 0
B4 FF FF FF FF FF 6F BC                  CD: 40 track: 0   min: 0 sek: 0
FE FF FF FF 6F BC B4 2C                  CD: 40 track: 0   min: 0 sek: 90
B4 BE FE FB 2B 87 FF BC                  CD: 1 track: 1   min: 4 sek: D4
B4 2B E6 6E 87 D7 FF BC                  CD: 94 track: 19   min: 91 sek: 78
B4 2A EA AE 9A BC FE 6F                  CD: 95 track: 15   min: 51 sek: 65
B4 BE FE FF FF FF 6F BC                  CD: 1 track: 1   min: 0 sek: 0
B4 2E EC CE AD DC FF BC                  CD: 91 track: 13   min: 31 sek: 52
B4 BE FE FF FF FF 6F BC                  CD: 1 track: 1   min: 0 sek: 0
B4 6D 0 FF FF FF FF BC                  CD: D2 track: FF   min: 0 sek: 0
F4 BE FE FF FC CE FF FC                  CD: 1 track: 1   min: 0 sek: 3
F4 2E EC CE AD DC FF FC                  CD: 91 track: 13   min: 31 sek: 52
F4 BE FE FF FF FF 8F FC                  CD: 1 track: 1   min: 0 sek: 0
F4 2E EC E7 56 EE 7F FE                  CD: 91 track: 13   min: 18 sek: A9
F4 BE FE FF FF FF 8F FC                  CD: 1 track: 1   min: 0 sek: 0
F4 EC FF BE FF FF 8F FC                  CD: 53 track: 0   min: 41 sek: 0
F4 BE FE FF FF FF 8F FC                  CD: 1 track: 1   min: 0 sek: 0
E9 7D FD FF FF FF 8F FC                  CD: C2 track: 2   min: 0 sek: 0
3A BE FE FF FF FF 87 BE                  CD: 1 track: 1   min: 0 sek: 0
3A BE FE FF FF FF C7 BE                  CD: 1 track: 1   min: 0 sek: 0
3A 5F 7F 7F FF FF C7 BE                  CD: E0 track: 80   min: 80 sek: 0
74 BE FE FF FF FF 8F 7C                  CD: 1 track: 1   min: 0 sek: 0
3A 5F FF 74 FF FF 8F 7C                  CD: E0 track: 0   min: 8B sek: 0
74 BE FE FF FF FF 8F 7C                  CD: 1 track: 1   min: 0 sek: 0
74 BE FE 7F FF FF C7 BE                  CD: 1 track: 1   min: 80 sek: 0
74 BE FE FF FF FF 8F 7C                  CD: 1 track: 1   min: 0 sek: 0
74 BE 7F 7F FF FF C7 BE                  CD: 1 track: 80   min: 80 sek: 0
74 BE FE FF FF FF 8F 7C                  CD: 1 track: 1   min: 0 sek: 0
E9 7D FD FF FF FF 1F 7C                  CD: C2 track: 2   min: 0 sek: 0
3A 5F 7F 7F FF FF C7 BE                  CD: E0 track: 80   min: 80 sek: 0
74 BE FE FF FF FF 8F 7C                  CD: 1 track: 1   min: 0 sek: 0
74 BE FE FF FF FF C7 BE                  CD: 1 track: 1   min: 0 sek: 0
74 BE FE FF FF FF 8F 7C                  CD: 1 track: 1   min: 0 sek: 0
74 7D FD FF FF FF 8F 7C                  CD: C2 track: 2   min: 0 sek: 0
3A BE FE FF FF FF 8F 7C                  CD: 1 track: 1   min: 0 sek: 0
3A BE FE FF FF FF 8F BE                  CD: 1 track: 1   min: 0 sek: 0
3A 5F 7F 7F FF FF C7 BE                  CD: E0 track: 80   min: 80 sek: 0
74 BE FE FF FF FF 8F 7C                  CD: 1 track: 1   min: 0 sek: 0
76 5F 7F 7F FF FF C7 BE                  CD: E0 track: 80   min: 80 sek: 0
74 BE FE FF FF FF 8F 7C                  CD: 1 track: 1   min: 0 sek: 0
74 BE FE FF FF FF C7 BE                  CD: 1 track: 1   min: 0 sek: 0
74 BE FE FF FF FF 8F 7C                  CD: 1 track: 1   min: 0 sek: 0
76 5F 7F 7F FF FF C7 BE                  CD: E0 track: 80   min: 80 sek: 0
74 BE FE FF FF FF 8F 7C                  CD: 1 track: 1   min: 0 sek: 0
74 BE FE FF FF FF C7 BE                  CD: 1 track: 1   min: 0 sek: 0
74 BE FE FF FF FF 8F 7C                  CD: 1 track: 1   min: 0 sek: 0
74 BF 7F 7F FF FF C7 BE                  CD: 0 track: 80   min: 80 sek: 0
74 BE FE FF FF FF 8F 7C                  CD: 1 track: 1   min: 0 sek: 0
74 5F 7F 7F FF FF C7 BE                  CD: E0 track: 80   min: 80 sek: 0
74 BE FE FF FF FF 8F 7C                  CD: 1 track: 1   min: 0 sek: 0
74 BE FE FF FF FF 8F BE                  CD: 1 track: 1   min: 0 sek: 0
74 BE FE FF FF FF 8F 7C                  CD: 1 track: 1   min: 0 sek: 0
74 7D FD FF FF FF 8F 7C                  CD: C2 track: 2   min: 0 sek: 0
3A 5F 7F 7F FF FF C7 BE                  CD: E0 track: 80   min: 80 sek: 0
74 BE FE FF FF FF 8F 7C                  CD: 1 track: 1   min: 0 sek: 0
74 BE FE FF FF FF 8F 7E                  CD: 1 track: 1   min: 0 sek: 0
74 BE FE FF FF FF 8F 7C                  CD: 1 track: 1   min: 0 sek: 0
E9 7D FD FF FF FF 1F 7C                  CD: C2 track: 2   min: 0 sek: 0
3A 5F 7F 7F FF FF C7 BE                  CD: E0 track: 80   min: 80 sek: 0
74 BE FE FF FF FF 87 BE                  CD: 1 track: 1   min: 0 sek: 0
74 FF 8F 7D FF FF C7 BE                  CD: 40 track: 70   min: 82 sek: 0
74 BE FE FF FF FF C7 BE                  CD: 1 track: 1   min: 0 sek: 0
74 BE FE FF FF FF 8F 7C                  CD: 1 track: 1   min: 0 sek: 0
74 BE FE FF FF FF 87 BE                  CD: 1 track: 1   min: 0 sek: 0
74 BE FE FF FF FF 8F 7C                  CD: 1 track: 1   min: 0 sek: 0
74 BE 7F 7F FF FF C7 BE                  CD: 1 track: 80   min: 80 sek: 0
74 BE FE FF FF FF 8F 7C                  CD: 1 track: 1   min: 0 sek: 0
74 BE FE FF FF FF C7 BE                  CD: 1 track: 1   min: 0 sek: 0
74 BE FE FF FF FF 8F 7C                  CD: 1 track: 1   min: 0 sek: 0
74 BE FF 7F FF FF C7 BE                  CD: 1 track: 0   min: 80 sek: 0
74 BE FE FF FF FF 8F 7C                  CD: 1 track: 1   min: 0 sek: 0
7A 5F 7F 7F FF FF C7 BE                  CD: E0 track: 80   min: 80 sek: 0
74 BE FE FF FF FF 8F 7C                  CD: 1 track: 1   min: 0 sek: 0
74 7D FD FF FF FF C7 DE                  CD: C2 track: 2   min: 0 sek: 0
3A 5F 7F 7F FF FF C7 BE                  CD: E0 track: 80   min: 80 sek: 0
74 BE FE FF FF FF 8F 7C                  CD: 1 track: 1   min: 0 sek: 0
74 5F 7F 7F FF FF C7 BE                  CD: E0 track: 80   min: 80 sek: 0
532C08F7 - enable MK
74 BE FE FF FF FF 8F 7C                  CD: 1 track: 1   min: 0 sek: 0
94 2E EC CE AD DC FF 9C                  CD: 91 track: 13   min: 31 sek: 52
532C14EB - end cmd/next cd 
94 BE FE FF FF FF EF 9C                  CD: 1 track: 1   min: 0 sek: 0
B4 DA 0 FF FF FF FF BC                  CD: 65 track: FF   min: 0 sek: 0
5A 5F 7F 7F FF FF F7 DE                  CD: E0 track: 80   min: 80 sek: 0
B4 2C 98 B4 FF FF EF BC                  CD: 93 track: 67   min: 4B sek: 0
B4 BE FE FF FF FF EF BC                  CD: 1 track: 1   min: 0 sek: 0
B4 2A EA AE 9A DA FF BC                  CD: 95 track: 15   min: 51 sek: 65
34 BE FE FF FF FF EF 3C                  CD: 1 track: 1   min: 0 sek: 0
34 29 E8 8E 86 CF FF 34                  CD: 96 track: 17   min: 71 sek: 79
34 FF DE 9D 5B BC FF 3C                  CD: 40 track: 21   min: 62 sek: A4
CE AD DE 7F 9E 1A 5F 7F                  CD: 12 track: 21   min: 80 sek: 61
34 FF FF BE FF FF EF 3C                  CD: 40 track: 0   min: 41 sek: 0
34 BE FE FF FF FF EF 3C                  CD: 1 track: 1   min: 0 sek: 0
532C08F7 - enable MK
34 2D F3 37 43 EB FF 9E                  CD: 92 track: C   min: C8 sek: BC
14 5F 7F 7F FF FF F7 8E                  CD: E0 track: 80   min: 80 sek: 0
532C14EB - end cmd/next cd
14 AE FF FF FF FF EF 3C                  CD: 11 track: 0   min: 0 sek: 0
FF FF FF EF 3C 34 29 E8                  CD: 40 track: 0   min: 10 sek: C3
34 BE FF EF EC DC FF 3C                  CD: 1 track: 0   min: 10 sek: 13
34 2E EC CE AD DC FF 3C                  CD: 91 track: 13   min: 31 sek: 52
34 6D 0 FF FF 78 FE FF                  CD: D2 track: FF   min: 0 sek: 0
34 7F 7F FF FF F7 9E 3C                  CD: C0 track: 80   min: 0 sek: 0
3C 34 BE FE FF FF FF 2B                  CD: 8B track: 41   min: 1 sek: 0
34 F FE FF FF FF EF 3C                  CD: B0 track: 1   min: 0 sek: 0
FE FF FF FF F7 9E 1A 15                  CD: 40 track: 0   min: 0 sek: 8
34 BE FE FF 3C 29 CF 3C                  CD: 1 track: 1   min: 0 sek: C3
34 29 E8 8E 86 CF FF 3C                  CD: 96 track: 17   min: 71 sek: 79
34 2E EC CE AD FE 68 FF                  CD: 91 track: 13   min: 31 sek: 52
532C08F7 - enable MK
34 5F 7F 7F FF FF F7 9E                  CD: E0 track: 80   min: 80 sek: 0
532C14EB - end cmd/next cd
14 BE FE FF FF FF EF 1C                  CD: 1 track: 1   min: 0 sek: 0
34 BE FE FF FF FF EF 3C                  CD: 1 track: 1   min: 0 sek: 0
34 2B E6 6E 87 78 FE FF                  CD: 94 track: 19   min: 91 sek: 78
34 BF 7F 7F FF FF F7 9E                  CD: 0 track: 80   min: 80 sek: 0
34 BE FE FF FF FF EF 29                  CD: 1 track: 1   min: 0 sek: 0
34 8E FF BF FF FF EF 3C                  CD: 31 track: 0   min: 40 sek: 0
BE FE FF FF FF EF 3C 34                  CD: 41 track: 0   min: 0 sek: 0
36 5F 7F FF 9E D0 FF 3C                  CD: E0 track: 80   min: 0 sek: 61
34 6D 0 FF FF FF FF 3C                  CD: D2 track: FF   min: 0 sek: 0
34 2C E8 8E 98 CE 34 FF                  CD: 93 track: 17   min: 71 sek: 67
69 BF FF FB CF 1C FF 3C                  CD: 0 track: 0   min: 4 sek: 30
73 FC F0 D2 FB FB FF FF                  CD: 43 track: F   min: 2D sek: 4
532C08F7 - enable MK
34 2E EC CE AD DC FF 3C                  CD: 91 track: 13   min: 31 sek: 52
14 2E EC CE AD DC FF 14                  CD: 91 track: 13   min: 31 sek: 52
532C14EB - end cmd/next cd
14 BE FE FF FF FF AE 1C                  CD: 1 track: 1   min: 0 sek: 0
34 BE FE FF FF FF AE 2E                  CD: 1 track: 1   min: 0 sek: 0
34 CE FF FF FF FF CF 3C                  CD: 71 track: 0   min: 0 sek: 0
FE FF FF FF CF 3C 34 BE                  CD: 40 track: 0   min: 0 sek: 30
36 5F 7F E7 FE FF CF 3C                  CD: E0 track: 80   min: 18 sek: 1
34 BE FE FF FF FF CF 3C                  CD: 1 track: 1   min: 0 sek: 0
34 BE 7F 7F FF 7F E7 9E                  CD: 1 track: 80   min: 80 sek: 0
34 BE FE FF FE FF CF 3C                  CD: 1 track: 1   min: 0 sek: 1
34 BE FE FF FF 7F E7 9E                  CD: 1 track: 1   min: 0 sek: 0
34 BE FE FF FE FF CF 3C                  CD: 1 track: 1   min: 0 sek: 1
34 BE FE FF FD FF CF 3C                  CD: 1 track: 1   min: 0 sek: 2
34 BE FE FF FD FF E7 9E                  CD: 1 track: 1   min: 0 sek: 2
34 BE FE FF FD FF CF 3C                  CD: 1 track: 1   min: 0 sek: 2
6C BE FE FF FD FF CF 3C                  CD: 1 track: 1   min: 0 sek: 2
1A 7E FE FF FD FF E7 9C                  CD: C1 track: 1   min: 0 sek: 2
D 5F 7F 7F FE FF E7 9E                  CD: E0 track: 80   min: 80 sek: 1
1A 5F 7F 7F FE FF E7 9E                  CD: E0 track: 80   min: 80 sek: 1
34 BE FE FF FD FF CF BE                  CD: 1 track: 1   min: 0 sek: 2
A5 FE FF FD FF CF 3C 34                  CD: 41 track: 0   min: 2 sek: 0
4B 7F 7F FE FF E7 9E 1C                  CD: C0 track: 80   min: 1 sek: 0
97 7F 7F FE FF E7 9E 18                  CD: C0 track: 80   min: 1 sek: 0
5F 7F 7F FE FF E7 9E BE                  CD: C0 track: 80   min: 1 sek: 0
5F FE 9E 1A FD FF CF 3C                  CD: 41 track: 61   min: E5 sek: 2
FD FF CF 3C 34 BE FE FF                  CD: 40 track: 30   min: C3 sek: CB
34 FE FF 34 FC FF CF 3C                  CD: 41 track: 0   min: CB sek: 3
34 7D FD FF F9 FF 8F 3C                  CD: C2 track: 2   min: 0 sek: 6
1A 5F 7F 7F FE 7F E7 9E                  CD: E0 track: 80   min: 80 sek: 1
34 BE FE FF FC FF E7 9E                  CD: 1 track: 1   min: 0 sek: 3
34 BE FE FF FC FF CF 3C                  CD: 1 track: 1   min: 0 sek: 3
34 BE FE FF FE 7F E7 9E                  CD: 1 track: 1   min: 0 sek: 1
34 BE FE FF FC FF E7 9E                  CD: 1 track: 1   min: 0 sek: 3
34 BE FE FF FC FF CF 3C                  CD: 1 track: 1   min: 0 sek: 3
34 BE FE FF FB FF CF 3C                  CD: 1 track: 1   min: 0 sek: 4
34 7C FE FF FB FF CF 3C                  CD: C3 track: 1   min: 0 sek: 4
1A 5F 7F 7F FD FF E7 9E                  CD: E0 track: 80   min: 80 sek: 2
34 BE FF 7F FD FF E7 9F                  CD: 1 track: 0   min: 80 sek: 2
34 BE FE FF FB FF CF 3C                  CD: 1 track: 1   min: 0 sek: 4
34 BE FE FF FA FF CF 3C                  CD: 1 track: 1   min: 0 sek: 5
532C08F7 - enable MK
14 BE FD FF FF FF AE 1C                  CD: 1 track: 2   min: 0 sek: 0
532C14EB - end cmd/next cd
34 5F 7E FF FF FF D7 1E                  CD: E0 track: 81   min: 0 sek: 0
34 BE FD FF FF FF AE 3C                  CD: 1 track: 2   min: 0 sek: 0
34 BE FD FF FF FF CF 3C                  CD: 1 track: 2   min: 0 sek: 0
3A 5F 7E FF FF FF E7 9E                  CD: E0 track: 81   min: 0 sek: 0
34 BE FD FF FF FF CF 3C                  CD: 1 track: 2   min: 0 sek: 0
34 BE FD FF FF FF CF 9E                  CD: 1 track: 2   min: 0 sek: 0
34 BE FD FF FF FF CF 3C                  CD: 1 track: 2   min: 0 sek: 0
34 BE FD FF FE FF CF 3C                  CD: 1 track: 2   min: 0 sek: 1
532C08F7 - enable MK
14 BE FC FF FF FF AE 1C                  CD: 1 track: 3   min: 0 sek: 0
532C14EB - end cmd/next cd
34 BE FC FF FF FF AE 3C                  CD: 1 track: 3   min: 0 sek: 0
34 BE FC FF FF FF CF 3C                  CD: 1 track: 3   min: 0 sek: 0
34 BE FC FF FF FF E7 9E                  CD: 1 track: 3   min: 0 sek: 0
34 BE FC FF FF FF CF 3C                  CD: 1 track: 3   min: 0 sek: 0
532C08F7 - enable MK
14 BE FB FF FF FF AE 1C                  CD: 1 track: 4   min: 0 sek: 0
532C14EB - end cmd/next cd
34 BE FB FF FF FF AE 3C                  CD: 1 track: 4   min: 0 sek: 0
34 BE FB FF FF FF CF 3C                  CD: 1 track: 4   min: 0 sek: 0
34 BE FB FF FF FF CF 9E                  CD: 1 track: 4   min: 0 sek: 0
34 BE FB FF FF FF CF 3C                  CD: 1 track: 4   min: 0 sek: 0
532C08F7 - enable MK
14 BE FA FF FF FF AE 1C                  CD: 1 track: 5   min: 0 sek: 0
532C14EB - end cmd/next cd
34 BE FA FF FF FF AE 3C                  CD: 1 track: 5   min: 0 sek: 0
34 BE FA FF FF FF CF 3C                  CD: 1 track: 5   min: 0 sek: 0
532C7887 - down
14 BE FB FF FF FF CF 1C                  CD: 1 track: 4   min: 0 sek: 0
14 BE FB FF FF FF AE 1C                  CD: 1 track: 4   min: 0 sek: 0
532C14EB - end cmd/next cd
34 BE FB FF FF FF AE 3C                  CD: 1 track: 4   min: 0 sek: 0
34 BE FB FF FF FF CF 3C                  CD: 1 track: 4   min: 0 sek: 0
1A 7E FB FF FF FF CF 3C                  CD: C1 track: 4   min: 0 sek: 0
D BE FB FF FF FF CF 3C                  CD: 1 track: 4   min: 0 sek: 0
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
34 BE FB FF F9 FF CF 9E                  CD: 1 track: 4   min: 0 sek: 6
34 BE FB FF F9 FF CF 3C                  CD: 1 track: 4   min: 0 sek: 6
532C08F7 - enable MK
14 BE FA FF FF FF AF E                  CD: 1 track: 5   min: 0 sek: 0
532C14EB - end cmd/next cd
16 5F 7D 7F FF FF D7 E                  CD: E0 track: 82   min: 80 sek: 0
14 BE FA FF FF FF AE 1C                  CD: 1 track: 5   min: 0 sek: 0
34 BE FA FF FF FF AE 3C                  CD: 1 track: 5   min: 0 sek: 0
34 BE FA FF FF FF CF 3C                  CD: 1 track: 5   min: 0 sek: 0
34 7D F5 FF FF FF 8F 3C                  CD: C2 track: A   min: 0 sek: 0
1A 5F 7D 7F FF FF E7 9E                  CD: E0 track: 82   min: 80 sek: 0
34 BE FA FF FF FF CF 3C                  CD: 1 track: 5   min: 0 sek: 0
36 5F 7D 7F FF FF E7 9E                  CD: E0 track: 82   min: 80 sek: 0
34 BE FA FF FF FF CF 3C                  CD: 1 track: 5   min: 0 sek: 0
34 BE FA FF FE FF CF 3C                  CD: 1 track: 5   min: 0 sek: 1
34 BE FA FF FE FF C7 9E                  CD: 1 track: 5   min: 0 sek: 1
34 BE FA FF FE FF CF 3C                  CD: 1 track: 5   min: 0 sek: 1
34 BF 7D 7F FF 7F E7 9E                  CD: 0 track: 82   min: 80 sek: 0
34 BE FA FF FE FF CF 3C                  CD: 1 track: 5   min: 0 sek: 1
34 5F 7D 7F FF 7F E7 9E                  CD: E0 track: 82   min: 80 sek: 0
34 BE FA FF FD FF CF 3C                  CD: 1 track: 5   min: 0 sek: 2
34 BE 7D 7F FE FF E7 9E                  CD: 1 track: 82   min: 80 sek: 1
34 BE FA FF FD FF CF 3C                  CD: 1 track: 5   min: 0 sek: 2
34 BE FA FF FD FF CF 9E                  CD: 1 track: 5   min: 0 sek: 2
34 BE FA FF FD FF CF 3C                  CD: 1 track: 5   min: 0 sek: 2
34 BF 7D 7F FE FF E7 9E                  CD: 0 track: 82   min: 80 sek: 1
34 BE FA FF FD FF C7 9E                  CD: 1 track: 5   min: 0 sek: 2
34 BE FA FF FD FF CF 3C                  CD: 1 track: 5   min: 0 sek: 2
34 BE FA FF FC FF CF 3C                  CD: 1 track: 5   min: 0 sek: 3
1A 5F 7D 7F FE 7F E7 9F                  CD: E0 track: 82   min: 80 sek: 1
34 BE FA FF FC FF CF 3C                  CD: 1 track: 5   min: 0 sek: 3
34 7D F5 FF F9 FF 9E 7C                  CD: C2 track: A   min: 0 sek: 6
1A 5F 7D 7F FE 7F E7 9E                  CD: E0 track: 82   min: 80 sek: 1
34 BE FA FF FC FF CF 3C                  CD: 1 track: 5   min: 0 sek: 3
34 BE FA FF FB FF CF 3C                  CD: 1 track: 5   min: 0 sek: 4
34 5F 7D 7F FD FF E7 9E                  CD: E0 track: 82   min: 80 sek: 2
34 BE FA FF FB FF CF 3C                  CD: 1 track: 5   min: 0 sek: 4
34 BE FA FF FA FF CF 3C                  CD: 1 track: 5   min: 0 sek: 5
34 BE FA FF FD 7F E7 9E                  CD: 1 track: 5   min: 0 sek: 2
34 BE FA FF FA FF CF 3C                  CD: 1 track: 5   min: 0 sek: 5
34 BE FA FF F9 FF CF 3C                  CD: 1 track: 5   min: 0 sek: 6
34 5F 7D 7F FC FF E7 9E                  CD: E0 track: 82   min: 80 sek: 3
34 BE FD 7F FC FF E7 9E                  CD: 1 track: 2   min: 80 sek: 3
34 BE FA FF F9 FF CF 3C                  CD: 1 track: 5   min: 0 sek: 6
34 BE FA FF F8 FF CF 3C                  CD: 1 track: 5   min: 0 sek: 7
532C18E7 - disable
94 29 E8 8E 86 CF FF 9C                  CD: 96 track: 17   min: 71 sek: 79
532C14EB - end cmd/next cd
94 B9 FE FF FF FF 6F 9C                  CD: 6 track: 1   min: 0 sek: 0
B4 2E EC CE AD DC FF BC                  CD: 91 track: 13   min: 31 sek: 52
B4 B9 FE FF FF FF 6F BC                  CD: 6 track: 1   min: 0 sek: 0
B4 6D 0 FF BC FF FF BC                  CD: D2 track: FF   min: 0 sek: 43
B4 B9 FE FF FF FF 6F BC                  CD: 6 track: 1   min: 0 sek: 0
B4 B9 FE FF FF FF B4 E6                  CD: 6 track: 1   min: 0 sek: 0
B4 87 FF FF FF FF 6F BC                  CD: 38 track: 0   min: 0 sek: 0
FF FF FF 6F BC B4 2A EA                  CD: 40 track: 0   min: 90 sek: 43
B4 B9 FF 6F 29 CF FF BC                  CD: 6 track: 0   min: 90 sek: D6
B4 29 E8 8E 86 CF FF BC                  CD: 96 track: 17   min: 71 sek: 79
B4 2E EC 56 BC FE FF BC                  CD: 91 track: 13   min: A9 sek: 43
B4 B9 FE FF FF FF 6F BC                  CD: 6 track: 1   min: 0 sek: 0
B4 2C E8 8E 98 CE FF BC                  CD: 93 track: 17   min: 71 sek: 67
B4 B9 FE FF FF FF 6F BC                  CD: 6 track: 1   min: 0 sek: 0
B4 2B E6 6E 87 D7 FF BC                  CD: 94 track: 19   min: 91 sek: 78
B4 FF 6F 2A 9A DA FF BC                  CD: 40 track: 90   min: D5 sek: 65
B4 2A EA AE 9A DA FF BC                  CD: 95 track: 15   min: 51 sek: 65
B4 29 8E FF B9 FF 6F BC                  CD: 96 track: 71   min: 0 sek: 46
B4 B9 FE FF FF FF 6F BC                  CD: 6 track: 1   min: 0 sek: 0
B4 6D 0 FF FF FF FF BC                  CD: D2 track: FF   min: 0 sek: 0
B4 B9 FE FF FF FF 6F BC                  CD: 6 track: 1   min: 0 sek: 0
B4 2C E8 8E 98 CE FF BC                  CD: 93 track: 17   min: 71 sek: 67
B4 FF DF 5F 43 EB FF DE                  CD: 40 track: 20   min: A0 sek: BC
B4 2B F3 37 43 EB FF DE                  CD: 94 track: C   min: C8 sek: BC
B4 2A 9A BC B9 FF 6F BC                  CD: 95 track: 65   min: 43 sek: 46
B4 B9 FE FF FF FF 6F BC                  CD: 6 track: 1   min: 0 sek: 0
9A 5C FF 7F FF B7 77 DC                  CD: E3 track: 0   min: 80 sek: 0
B4 2E EC CE AD DC FF BC                  CD: 91 track: 13   min: 31 sek: 52
B4 6D 0 FF FF FF FF B4                  CD: D2 track: FF   min: 0 sek: 0
B4 FF 6F 8E 98 CE FF BC                  CD: 40 track: 90   min: 71 sek: 67
8E 98 CE FF BC B4 B9 FE                  CD: 27 track: 31   min: 0 sek: 43
B4 F3 EB B4 FF FF 6F BC                  CD: 4C track: 14   min: 4B sek: 0
B4 B9 FE FF FF FF 6F BC                  CD: 6 track: 1   min: 0 sek: 0
B4 29 E8 8E 86 CF FF BC                  CD: 96 track: 17   min: 71 sek: 79
B4 B9 FE FF FF FF 6F BC                  CD: 6 track: 1   min: 0 sek: 0
B4 2E EC CE AD DC BC FE                  CD: 91 track: 13   min: 31 sek: 52
B4 FF 6F BC FF FF FF BC                  CD: 40 track: 90   min: 43 sek: 0
FF FF FF BC B4 B9 FE FF                  CD: 40 track: 0   min: 43 sek: 4B
B4 23 FF FE FF FF 6F BC                  CD: 9C track: 0   min: 1 sek: 0
B9 FE FF FF FF 6F BC B4                  CD: 41 track: 0   min: 0 sek: 0
B4 B9 FE FF BC 2A DA BC                  CD: 6 track: 1   min: 0 sek: 43
B4 2A EA AE 9A DA FF BC                  CD: 95 track: 15   min: 51 sek: 65
B4 29 E8 8E 86 CF B9 FF                  CD: 96 track: 17   min: 71 sek: 79
B4 7F FF FF B7 DE 7F BC                  CD: C0 track: 0   min: 0 sek: 48
FF 79 69 73 FD FF FF FE                  CD: C6 track: 96   min: 8C sek: 2
B4 FF FF FF FF FF 6F BC                  CD: 40 track: 0   min: 0 sek: 0
FE FF FF FF 6F BC B4 2C                  CD: 40 track: 0   min: 0 sek: 90
B4 B9 FE FF 2B 6E FF BC                  CD: 6 track: 1   min: 0 sek: D4
B4 2B E6 6E 87 D7 FF BC                  CD: 94 track: 19   min: 91 sek: 78
B4 2A EA AE 9A BC FE FF                  CD: 95 track: 15   min: 51 sek: 65
B4 B9 FE FF FF FF 6F BC                  CD: 6 track: 1   min: 0 sek: 0
B4 2E EC CE AD DC FF BC                  CD: 91 track: 13   min: 31 sek: 52
B4 B9 FE FF FF FF 6F BC                  CD: 6 track: 1   min: 0 sek: 0
B4 6D 0 FF FF FF FF BC                  CD: D2 track: FF   min: 0 sek: 0
B4 B9 FE FF BC E8 CE BC                  CD: 6 track: 1   min: 0 sek: 43
B4 2C E8 8E 98 CE FF BC                  CD: 93 track: 17   min: 71 sek: 67
B4 2B E6 6E 87 D7 B4 FF                  CD: 94 track: 19   min: 91 sek: 78
B4 B9 FE FF FF FF 6F BC                  CD: 6 track: 1   min: 0 sek: 0
B4 B9 FE FF FF FF EF BC                  CD: 6 track: 1   min: 0 sek: 0
B4 E8 FF FE FF FF F7 DE                  CD: 57 track: 0   min: 1 sek: 0
B4 BC FF 7F FF FF F7 DE                  CD: 3 track: 0   min: 80 sek: 0
B4 B9 FE FF FF B4 FF BC                  CD: 6 track: 1   min: 0 sek: 0
B4 6D 0 FF FF FF FF BC                  CD: D2 track: FF   min: 0 sek: 0
B4 2C E8 8E 98 CE FF BC                  CD: 93 track: 17   min: 71 sek: 67
B4 FE FF 66 87 D7 FF 3C                  CD: 41 track: 0   min: 99 sek: 78
E6 6E 87 D7 FF 3C 34 B9                  CD: D1 track: 78   min: 28 sek: 0
34 2A 9A FF B9 FF EF 3C                  CD: 95 track: 65   min: 0 sek: 46
34 B9 FE FF FF FF EF 3C                  CD: 6 track: 1   min: 0 sek: 0
34 F9 FE FF FF E7 EC AD                  CD: 46 track: 1   min: 0 sek: 0
34 CE AD DC FF 3C EF 3C                  CD: 71 track: 52   min: 23 sek: 0
EF 3C 34 6D 0 FF FF FF                  CD: 83 track: CB   min: 92 sek: FF
34 FF 3C 8E 98 CE FF 3C                  CD: 40 track: C3   min: 71 sek: 67
2C E8 8E 98 CE FF 3C 34                  CD: 57 track: 71   min: 67 sek: 31
34 E6 D7 34 FF FF EF 3C                  CD: 59 track: 28   min: CB sek: 0
34 B9 FE FF FF FF EF 3C                  CD: 6 track: 1   min: 0 sek: 0
34 29 E8 8E 86 CF FF 3C                  CD: 96 track: 17   min: 71 sek: 79
34 B9 FE FF FF FF EF 3C                  CD: 6 track: 1   min: 0 sek: 0
34 2E EC CE AD DC 3C B9                  CD: 91 track: 13   min: 31 sek: 52
34 BF FF EF 3C FF FF 3C                  CD: 0 track: 0   min: 10 sek: C3
FF FF 3C 34 B9 FE FF FF                  CD: 40 track: C3   min: CB sek: 46
34 8E FF FF FF FF EF 3C                  CD: 31 track: 0   min: 0 sek: 0
FE FF FF FF EF 3C 34 2B                  CD: 40 track: 0   min: 0 sek: 10
34 B9 FE FF 3C EA FF 3C                  CD: 6 track: 1   min: 0 sek: C3
34 2A EA AE 9A DA FF 3C                  CD: 95 track: 15   min: 51 sek: 65
34 29 E8 8E 86 CF 34 FF                  CD: 96 track: 17   min: 71 sek: 79
34 FF FF FF EF 3C FF 3C                  CD: 40 track: 0   min: 0 sek: 10
FF 3C 34 B9 FE FF FF 34                  CD: 83 track: CB   min: 46 sek: 1
34 FF FF FF FF FF EF 3C                  CD: 40 track: 0   min: 0 sek: 0
532C38C7 - SEEKFORWARD MK
FE FF FF FF EF 3C 34 94                  CD: 40 track: 0   min: 0 sek: 10
532C14EB - end cmd/next cd
94 BE FE FF FF FF 6F 9C                  CD: 1 track: 1   min: 0 sek: 0
B4 BE FE FF FF FF 6F B4                  CD: 1 track: 1   min: 0 sek: 0
B4 AE FF FE FF FF 6F BC                  CD: 11 track: 0   min: 1 sek: 0
BE FE FF FF FF 6F BC B4                  CD: 41 track: 0   min: 0 sek: 0
B4 BE FE FF FF 2E AD BC                  CD: 1 track: 1   min: 0 sek: 0
B4 2E EC CE AD DC FF BC                  CD: 91 track: 13   min: 31 sek: 52
B4 6D 0 FF FF FF BC FE                  CD: D2 track: FF   min: 0 sek: 0
B4 FF 6F BC 98 CE FF BC                  CD: 40 track: 90   min: 43 sek: 67
98 CE FF BC B4 BE FE FF                  CD: 71 track: 0   min: 43 sek: 4B
B4 87 BC FE FF FF 6F BC                  CD: 38 track: 43   min: 1 sek: 0
B4 BE FE FF FF FF 6F BC                  CD: 1 track: 1   min: 0 sek: 0
B4 5F 7F 7F FF F5 8E BC                  CD: E0 track: 80   min: 80 sek: 0
B4 29 E8 8E 86 CF FF BC                  CD: 96 track: 17   min: 71 sek: 79
B4 2E EC CE ED DC B4 FF                  CD: 91 track: 13   min: 31 sek: 12
B4 FD FF FF FE DF 79 BC                  CD: 42 track: 0   min: 0 sek: 1
DE 5A 5F 7F 7F FF FF B7                  CD: E5 track: A0   min: 80 sek: 80
B4 98 BC FF FF FE CF BC                  CD: 27 track: 43   min: 0 sek: 0
BE FE FF FF FF 67 DE 5A                  CD: 41 track: 0   min: 0 sek: 0
B4 BE FE FF B4 AE FF BC                  CD: 1 track: 1   min: 0 sek: 4B
B4 2A EA AE 9A DA FF BC                  CD: 95 track: 15   min: 51 sek: 65
B4 29 E8 8E 86 BC FE FF                  CD: 96 track: 17   min: 71 sek: 79
B4 BE FE FF FF FF 6F BC                  CD: 1 track: 1   min: 0 sek: 0
B4 6D 0 FF FF FF FF BC                  CD: D2 track: FF   min: 0 sek: 0
B4 BE FE FF FF FF 6F BC                  CD: 1 track: 1   min: 0 sek: 0
B4 2C E8 8E 98 CE FF BC                  CD: 93 track: 17   min: 71 sek: 67
B4 BE FE FF BC E6 AF BC                  CD: 1 track: 1   min: 0 sek: 43
B4 2B E6 6E 87 D7 FF BC                  CD: 94 track: 19   min: 91 sek: 78
B4 2A EA AE 9A 6B B4 FF                  CD: 95 track: 15   min: 51 sek: 65
B4 FE FF FF FF 6F BC BC                  CD: 41 track: 0   min: 0 sek: 0
BC B4 BE FE FF FF FF 6F                  CD: B track: 41   min: 1 sek: 0
B4 CE FF FE FF FF 6F BC                  CD: 71 track: 0   min: 1 sek: 0
BE FE FF FF FF 6F BC B4                  CD: 41 track: 0   min: 0 sek: 0
B4 BE FE FF 6F E8 98 BC                  CD: 1 track: 1   min: 0 sek: 90
B4 2C E8 8E 98 CE FF BC                  CD: 93 track: 17   min: 71 sek: 67
B4 2B E6 6E 87 FF B4 FF                  CD: 94 track: 19   min: 91 sek: 78
B4 FE FF FF FF 6F BC BC                  CD: 41 track: 0   min: 0 sek: 0
BC B4 BE FE FF FF FF 6F                  CD: B track: 41   min: 1 sek: 0
B4 A1 BC BE FF FF 6F BC                  CD: 1E track: 43   min: 41 sek: 0
B4 BE FE FF FF FF 6F BC                  CD: 1 track: 1   min: 0 sek: 0
B4 6D 0 FF FF FF FF BC                  CD: D2 track: FF   min: 0 sek: 0
B4 BE FE FF FF FF 77 DE                  CD: 1 track: 1   min: 0 sek: 0
B4 2C E8 8E 98 CE FF B4                  CD: 93 track: 17   min: 71 sek: 67
B4 FF 6F 6E 87 D7 FF BC                  CD: 40 track: 90   min: 91 sek: 78
6E 87 D7 FF BC B4 BE FE                  CD: 38 track: 28   min: 0 sek: 43
B4 AF 7F FE FF FF 6F BC                  CD: 10 track: 80   min: 1 sek: 0
B4 BE FE FF FF FF 6F BC                  CD: 1 track: 1   min: 0 sek: 0
B4 2E EC CE AD DC FF BC                  CD: 91 track: 13   min: 31 sek: 52
B4 BE FE FF FF FF 6F BC                  CD: 1 track: 1   min: 0 sek: 0
B4 6D 0 FF FF FF FF B4                  CD: D2 track: FF   min: 0 sek: 0
B4 FF BC 8E 98 CE FF BC                  CD: 40 track: 43   min: 71 sek: 67
2C E8 8E 98 CE FF BC B4                  CD: 57 track: 71   min: 67 sek: 31
B4 E6 FF BE FF FF 6F BC                  CD: 59 track: 0   min: 41 sek: 0
B4 BE FE FF FF FF 6F BC                  CD: 1 track: 1   min: 0 sek: 0
B4 29 E8 8E 86 CF FF BC                  CD: 96 track: 17   min: 71 sek: 79
B4 BE FE FF FF FF 6F BC                  CD: 1 track: 1   min: 0 sek: 0
B4 2E EC CE AD DC FF DF                  CD: 91 track: 13   min: 31 sek: 52
B4 7F FF B7 DE FF FF BC                  CD: C0 track: 0   min: 48 sek: 21
FF FF BC B4 BE FE FF FF                  CD: 40 track: 43   min: 4B sek: 41
B4 8E BC FF FF FF EF BC                  CD: 31 track: 43   min: 0 sek: 0
BE FE FF FF FF EF BC B4                  CD: 41 track: 0   min: 0 sek: 0
B4 BE FE FF BC AE FF BC                  CD: 1 track: 1   min: 0 sek: 43
B4 2A EA AE 9A DA FF BC                  CD: 95 track: 15   min: 51 sek: 65
B4 29 E8 8E 86 FF BE EF                  CD: 96 track: 17   min: 71 sek: 79
B4 FE FF FF FF EF BC BC                  CD: 41 track: 0   min: 0 sek: 0
BC 34 BE FE FF FF FF EF                  CD: 8B track: 41   min: 1 sek: 0
34 FF FC FE FF FF EF 3C                  CD: 40 track: 3   min: 1 sek: 0
BE FE FF FF FF EF 3C 34                  CD: 41 track: 0   min: 0 sek: 0
34 BE FE FF FF 2B 87 3C                  CD: 1 track: 1   min: 0 sek: 0
34 2B E6 6E 87 D7 FF 3C                  CD: 94 track: 19   min: 91 sek: 78
34 2A EA AE 9A DA 3C BE                  CD: 95 track: 15   min: 51 sek: 65
34 FF FF FF EF 3C FF 3C                  CD: 40 track: 0   min: 0 sek: 10
FF 3C 34 BE FE FF FF FF                  CD: 83 track: CB   min: 41 sek: 1
34 CE FF BE FF FF EF 3C                  CD: 71 track: 0   min: 41 sek: 0
34 BE FE FF FF FF EF 3C                  CD: 1 track: 1   min: 0 sek: 0
36 16 74 47 4C 67 7F 9E                  CD: A9 track: 8B   min: B8 sek: B3
34 BE FE FF FF FF EF 3C                  CD: 1 track: 1   min: 0 sek: 0
34 2B E6 6E 87 D7 3C FE                  CD: 94 track: 19   min: 91 sek: 78
34 FF FF EF 3C DA FF 3C                  CD: 40 track: 0   min: 10 sek: C3
DA FF 3C 34 BE FE FF FF                  CD: 40 track: C3   min: CB sek: 41
34 8E FF FF FF FF EF 3C                  CD: 31 track: 0   min: 0 sek: 0
532C08F7 - enable MK
FF FF FF EF 3C 34 2E BE                  CD: 40 track: 0   min: 10 sek: C3
14 DF FE CF FF FF FF 1C                  CD: 60 track: 1   min: 30 sek: 0
532C14EB - end cmd/next cd
FF FF FF F1 C1 4B DF E8                  CD: 40 track: 0   min: E sek: 3E
34 E8 FF 3C FF FF EF 3C                  CD: 57 track: 0   min: C3 sek: 0
FF FF EF 3C 34 2B E6 6E                  CD: 40 track: 10   min: C3 sek: CB
34 FD FF 34 D3 DA FF 3C                  CD: 42 track: 0   min: CB sek: 2C
34 2A EA AE 9A DA FF 3C                  CD: 95 track: 15   min: 51 sek: 65
34 29 1D 3C BE FF EF 3C                  CD: 96 track: E2   min: C3 sek: 41
34 BE FD FF FF FF EF 3C                  CD: 1 track: 2   min: 0 sek: 0
34 6D 0 FF FF FF FF 3C                  CD: D2 track: FF   min: 0 sek: 0
34 BE FD FF FF FF EF 3C                  CD: 1 track: 2   min: 0 sek: 0
34 2C E8 8E 98 CE FF 3C                  CD: 93 track: 17   min: 71 sek: 67
34 FF EF E6 87 D7 FF 3C                  CD: 40 track: 10   min: 19 sek: 78
2B E6 6E 87 D7 FF 3C 34                  CD: 59 track: 91   min: 78 sek: 28
34 2E CE 3C BE FF AE 3C                  CD: 91 track: 31   min: C3 sek: 41
34 BE FD FF FF FF AE 3C                  CD: 1 track: 2   min: 0 sek: 0
34 2E EC CE AD DC FF 3C                  CD: 91 track: 13   min: 31 sek: 52
34 BE FD FF FF FF AE 3C                  CD: 1 track: 2   min: 0 sek: 0
34 2E EC CE AD DC FF 34                  CD: 91 track: 13   min: 31 sek: 52
34 FF AE 3C AD DC FF 3C                  CD: 40 track: 51   min: C3 sek: 52
AD DC FF 3C 34 BE FD FF                  CD: 63 track: 0   min: C3 sek: CB
34 FF AE BE FF FF AE 3C                  CD: 40 track: 51   min: 41 sek: 0
34 7D FB FF FF FF AE 3C                  CD: C2 track: 4   min: 0 sek: 0
1A 5F 7E FF FF FF D7 1E                  CD: E0 track: 81   min: 0 sek: 0
34 BE FD FF FF FF CF 3C                  CD: 1 track: 2   min: 0 sek: 0
34 BF 7E FF FF FF E7 9E                  CD: 0 track: 81   min: 0 sek: 0
34 BE FD FF FF FF CF 3C                  CD: 1 track: 2   min: 0 sek: 0
532C7887 - down
14 BE FD FF FF FF CF 1C                  CD: 1 track: 2   min: 0 sek: 0
14 BE FD FF FF FF AE 1C                  CD: 1 track: 2   min: 0 sek: 0
532C14EB - end cmd/next cd
34 BE FD FF FF FF CF 3C                  CD: 1 track: 2   min: 0 sek: 0
3A 5F 7E FF FF FF E7 9E                  CD: E0 track: 81   min: 0 sek: 0
34 BE FD FF FF FF CF 3C                  CD: 1 track: 2   min: 0 sek: 0
34 BE FD FF FF FF CF 3C                  CD: 1 track: 2   min: 0 sek: 0
1A 5F 7E FF FF FF E7 9E                  CD: E0 track: 81   min: 0 sek: 0
34 BE FD FF FF FF CF 3C                  CD: 1 track: 2   min: 0 sek: 0
34 BE FD FF FE FF CF 3C                  CD: 1 track: 2   min: 0 sek: 1
34 BE FD FF FE FF E7 9E                  CD: 1 track: 2   min: 0 sek: 1
34 BE FD FF FE FF CF 3C                  CD: 1 track: 2   min: 0 sek: 1
34 BE FD FF FD FF CF 3C                  CD: 1 track: 2   min: 0 sek: 2
34 BE FD FF FC FF CF 3C                  CD: 1 track: 2   min: 0 sek: 3
34 BE FD FF FE 7F E7 9E                  CD: 1 track: 2   min: 0 sek: 1
34 BE FD FF FC FF CF 3C                  CD: 1 track: 2   min: 0 sek: 3
532C7887 - down
34 5F 7E FF FE 7F E7 9E                  CD: E0 track: 81   min: 0 sek: 1
14 BE FD FF FF FF CF 1C                  CD: 1 track: 2   min: 0 sek: 0
14 BE FD FF FF FF AE 1C                  CD: 1 track: 2   min: 0 sek: 0
532C14EB - end cmd/next cd
34 BE FD FF FF FF AE 3C                  CD: 1 track: 2   min: 0 sek: 0
34 BE FD FF FF FF CF 3C                  CD: 1 track: 2   min: 0 sek: 0
34 BE FD FF FF FF C7 9E                  CD: 1 track: 2   min: 0 sek: 0
34 BE FD FF FF FF CF 3C                  CD: 1 track: 2   min: 0 sek: 0
34 BE FD FF FE FF CF 3C                  CD: 1 track: 2   min: 0 sek: 1
34 5F 7E FF FF 7F E7 9E                  CD: E0 track: 81   min: 0 sek: 0
34 BE FD FF FE FF CF 3C                  CD: 1 track: 2   min: 0 sek: 1
34 BE FD FF FD FF CF 3C                  CD: 1 track: 2   min: 0 sek: 2
34 BE FC FF FE FF E7 9E                  CD: 1 track: 3   min: 0 sek: 1
34 BE 7E FF FE FF E7 9E                  CD: 1 track: 81   min: 0 sek: 1
34 BE FD FF FD FF CF 3C                  CD: 1 track: 2   min: 0 sek: 2
532C58A7 - seekback
14 BE FD FF FC FF BF 1C                  CD: 1 track: 2   min: 0 sek: 3
532C14EB - end cmd/next cd
34 BE FD FF FC FF BF 3C                  CD: 1 track: 2   min: 0 sek: 3
34 BE FD FF FF FF BF 3C                  CD: 1 track: 2   min: 0 sek: 0
34 BE FE FC F8 FF BF 3C                  CD: 1 track: 1   min: 3 sek: 7
34 BE FE FC F9 FF BF 3C                  CD: 1 track: 1   min: 3 sek: 6
34 BE FE FC FA FF BF 3C                  CD: 1 track: 1   min: 3 sek: 5
34 BE FE FC FC FF BF 3C                  CD: 1 track: 1   min: 3 sek: 3
34 BE FE FF 78 F8 DF 9E                  CD: 1 track: 1   min: 0 sek: 87
34 BE FE FC 7F 7F DF 9E                  CD: 1 track: 1   min: 3 sek: 80
34 BE FE FC FF FF 3C DF                  CD: 1 track: 1   min: 3 sek: 0
34 7E BF 3C A8 FF BF 3C                  CD: C1 track: 40   min: C3 sek: 57
A8 FF BF 3C 34 BE FE FD                  CD: 40 track: 40   min: C3 sek: CB
34 FE BF FD AC FF BF 3C                  CD: 41 track: 40   min: 2 sek: 53
FE FD AC FF BF 3C 34 BE                  CD: 42 track: 53   min: 0 sek: 40
34 BE AE 3C FE FF BF 3C                  CD: 1 track: 51   min: C3 sek: 1
34 BE FE FD AF FF BF 3C                  CD: 1 track: 1   min: 2 sek: 50
34 BE FE FD B6 BF 34 FD                  CD: 1 track: 1   min: 2 sek: 49
BF 3C 34 BE FE FD BA FF                  CD: 83 track: CB   min: 41 sek: 1
BF 3C 34 BE FE FD BB FF                  CD: 83 track: CB   min: 41 sek: 1
BF 3C 34 FD BC FF BF 3C                  CD: 83 track: CB   min: 2 sek: 43
34 BE FE FD BE FF BF 3C                  CD: 1 track: 1   min: 2 sek: 41
34 BE FE FD BF FF BF 3C                  CD: 1 track: 1   min: 2 sek: 40
34 BE FE FD C7 FF BF 3C                  CD: 1 track: 1   min: 2 sek: 38
34 BE FE FD CA FF BF 3C                  CD: 1 track: 1   min: 2 sek: 35
34 BE FE FD CB FF BF 3C                  CD: 1 track: 1   min: 2 sek: 34
34 BE FE FD CC FF BF 3C                  CD: 1 track: 1   min: 2 sek: 33
34 BE FE FD CD FF BF 3C                  CD: 1 track: 1   min: 2 sek: 32
34 BE FE FD CF FF BF 3C                  CD: 1 track: 1   min: 2 sek: 30
34 BE FE FD D6 FF BF 3C                  CD: 1 track: 1   min: 2 sek: 29
34 BE FE FD D7 FF BF 3C                  CD: 1 track: 1   min: 2 sek: 28
34 BE FE FD FF 34 FD BF                  CD: 1 track: 1   min: 2 sek: 0
34 BF BF 76 7F EF CF 3C                  CD: 0 track: 40   min: 89 sek: 80
F0 D2 FB FB F7 73 FC FE                  CD: 6D track: 4   min: 4 sek: 8
34 FD BF FD DE FF BF 3C                  CD: 42 track: 40   min: 2 sek: 21
FE FD DE FF BF 3C 34 BE                  CD: 42 track: 21   min: 0 sek: 40
34 BE E6 34 FD FF BF 3C                  CD: 1 track: 19   min: CB sek: 2
34 BE FE FD E8 FF BF 3C                  CD: 1 track: 1   min: 2 sek: 17
34 BE FE FD FF 34 FD FF                  CD: 1 track: 1   min: 2 sek: 0
34 FE FD EB FF BF 3E 3C                  CD: 41 track: 2   min: 14 sek: 0
3C 34 BE FE FD ED FF 34                  CD: 8B track: 41   min: 1 sek: 2
34 FD BF FD EE FF BF 3C                  CD: 42 track: 40   min: 2 sek: 11
FE FD EE FF BF 3C 34 BE                  CD: 42 track: 11   min: 0 sek: 40
34 BE FD FF 34 F9 BF 3C                  CD: 1 track: 2   min: 0 sek: CB
34 BE FE FD F9 FF BF 3C                  CD: 1 track: 1   min: 2 sek: 6
34 BE FE FD FA FF 3C FD                  CD: 1 track: 1   min: 2 sek: 5
FE FD FC FF BF 3C 34 BE                  CD: 42 track: 3   min: 0 sek: 40
532C08F7 - enable MK
FE FD FE FF BF 3C 34 BE                  CD: 42 track: 1   min: 0 sek: 40
14 BE FE FD FF FF CF 1C                  CD: 1 track: 1   min: 2 sek: 0
532C14EB - end cmd/next cd
34 BE FE FD FF FF CF 3C                  CD: 1 track: 1   min: 2 sek: 0
34 BE FE FE A9 FF CF 3C                  CD: 1 track: 1   min: 1 sek: 56
34 BE FE FD FF FF E7 9E                  CD: 1 track: 1   min: 2 sek: 0
34 BE FE FD FF FF CF 3C                  CD: 1 track: 1   min: 2 sek: 0
34 BE FE FD FE FF CF 3C                  CD: 1 track: 1   min: 2 sek: 1
34 BE FE FD FE FF CF 9E                  CD: 1 track: 1   min: 2 sek: 1
34 BE FE FD FE FF CF 3C                  CD: 1 track: 1   min: 2 sek: 1
34 BE FE FD FD FF CF 3C                  CD: 1 track: 1   min: 2 sek: 2
36 5F 7F 7E FE FF E7 9E                  CD: E0 track: 80   min: 81 sek: 1
34 BE FE FD FD FF CF 3C                  CD: 1 track: 1   min: 2 sek: 2
34 BE FE FD FD FF CF 1E                  CD: 1 track: 1   min: 2 sek: 2
34 BE FE FD FD FF CF 3C                  CD: 1 track: 1   min: 2 sek: 2
34 BE FE FE FE FF E7 9E                  CD: 1 track: 1   min: 1 sek: 1
34 BE FE FD FD FF CF 3C                  CD: 1 track: 1   min: 2 sek: 2
34 BE FE FD FC FF CF 3C                  CD: 1 track: 1   min: 2 sek: 3
34 BF 7F 7E FE 7F E7 9E                  CD: 0 track: 80   min: 81 sek: 1
34 BE FE FD FC FF CF 3C                  CD: 1 track: 1   min: 2 sek: 3
34 BE FE FD FC FF CF 3E                  CD: 1 track: 1   min: 2 sek: 3
34 BE FE FD FC FF CF 3C                  CD: 1 track: 1   min: 2 sek: 3
34 BE FE FD FE 7F E7 9E                  CD: 1 track: 1   min: 2 sek: 1
34 BE FE FD FC FF CF 3C                  CD: 1 track: 1   min: 2 sek: 3
34 BE FE FD FC FF CF 1E                  CD: 1 track: 1   min: 2 sek: 3
34 7D FE FD FC FF CF 1E                  CD: C2 track: 1   min: 2 sek: 3
1A 5F 7F 7E FE 7F E7 9E                  CD: E0 track: 80   min: 81 sek: 1
34 BE FE FD FC FF CF 3C                  CD: 1 track: 1   min: 2 sek: 3
34 BE FE FD FB FF CF 3C                  CD: 1 track: 1   min: 2 sek: 4
34 BE FE FD FA FF CF 3C                  CD: 1 track: 1   min: 2 sek: 5
34 BE FE FD FB 7F E7 9E                  CD: 1 track: 1   min: 2 sek: 4
34 BE FE FD FA FF CF 3C                  CD: 1 track: 1   min: 2 sek: 5
34 BE FE FD F9 FF CF 3C                  CD: 1 track: 1   min: 2 sek: 6
32 5F 7F 7E FC FF E7 9E                  CD: E0 track: 80   min: 81 sek: 3
34 BE FE FD F9 FF CF 3C                  CD: 1 track: 1   min: 2 sek: 6
34 BE FE FD FC FF E7 9E                  CD: 1 track: 1   min: 2 sek: 3
34 BE FE FD F9 FF CF 3C                  CD: 1 track: 1   min: 2 sek: 6
34 BE FE FD F8 FF CF 3C                  CD: 1 track: 1   min: 2 sek: 7
34 BE FE FE FC 7F E7 9E                  CD: 1 track: 1   min: 1 sek: 3
34 BE FE FD F8 FF CF 3C                  CD: 1 track: 1   min: 2 sek: 7
34 BE FE FD F7 FF CF 3C                  CD: 1 track: 1   min: 2 sek: 8
74 BE FE FD F7 FF CF 3C                  CD: 1 track: 1   min: 2 sek: 8
1A 5F 7F 7E FB FF E7 9E                  CD: E0 track: 80   min: 81 sek: 4
34 BE FE FD F7 FF CF 3C                  CD: 1 track: 1   min: 2 sek: 8
34 BE FE FD F6 FF CF 3C                  CD: 1 track: 1   min: 2 sek: 9
532CD827 - seekforward
14 BE FE FD F6 FF BF 1C                  CD: 1 track: 1   min: 2 sek: 9
532C14EB - end cmd/next cd
34 BE FE FD F6 FF BF 3C                  CD: 1 track: 1   min: 2 sek: 9
34 BE FE FD EF FF BF 3C                  CD: 1 track: 1   min: 2 sek: 10
34 BE FE FD EE FF BF 3C                  CD: 1 track: 1   min: 2 sek: 11
34 BE FE FD ED FF BF 3C                  CD: 1 track: 1   min: 2 sek: 12
34 BE FE FD EB FF BF 3C                  CD: 1 track: 1   min: 2 sek: 14
34 BE FE FD EA FF BF 34                  CD: 1 track: 1   min: 2 sek: 15
BE FE FD E8 FF BF 3C 34                  CD: 41 track: 2   min: 17 sek: 0
BE FE FD E7 FF BF 3C 34                  CD: 41 track: 2   min: 18 sek: 0
BE FE FD E6 3C FE FF 3C                  CD: 41 track: 2   min: 19 sek: C3
BE FE FD DF FF BF 3C 34                  CD: 41 track: 2   min: 20 sek: 0
34 BE FE FD DC CF BE DC                  CD: 1 track: 1   min: 2 sek: 23
FF BF 3C 34 BE FE FD D9                  CD: 0 track: C3   min: CB sek: 41
FF BF 3C 34 BE FE FD D7                  CD: 0 track: C3   min: CB sek: 41
FF BF 3C 34 BE FE FD D6                  CD: 0 track: C3   min: CB sek: 41
FF BF 3C 34 BE FE FD CF                  CD: 0 track: C3   min: CB sek: 41
FF 7E 78 69 7D FD FB 9C                  CD: C1 track: 87   min: 96 sek: 82
1A 5F 7F 7E E6 FF DF FE                  CD: E0 track: 80   min: 81 sek: 19
34 99 7E 3D 8B FF BF 3C                  CD: 26 track: 81   min: C2 sek: 74
C5 FF DF 9E 1A 5F 7F 7E                  CD: 40 track: 20   min: 61 sek: E5
34 FD BF FD C6 FF BF 3C                  CD: 42 track: 40   min: 2 sek: 39
FD C6 FF BF 3C 34 BE FE                  CD: 79 track: 0   min: 40 sek: C3
34 BE FF 34 FE FF BF 3C                  CD: 1 track: 0   min: CB sek: 1
34 BE FE FD BE FF BF 3C                  CD: 1 track: 1   min: 2 sek: 41
34 BE FE FD BC BF BE FF                  CD: 1 track: 1   min: 2 sek: 43
34 FD BB FF BF 3C BF 3C                  CD: 42 track: 44   min: 0 sek: 40
BF 3C 34 BE FE FD B9 34                  CD: 83 track: CB   min: 41 sek: 1
34 FD BF FD B7 FF BF 3C                  CD: 42 track: 40   min: 2 sek: 48
FE FD B7 FF BF 3C 34 BE                  CD: 42 track: 48   min: 0 sek: 40
34 BE FD 3C FE DF BF 3C                  CD: 1 track: 2   min: C3 sek: 1
34 BE FE FD AA FF BF 3C                  CD: 1 track: 1   min: 2 sek: 55
34 BE FE FD A9 FF BF 3C                  CD: 1 track: 1   min: 2 sek: 56
34 BE FE FD A7 FF BF 3C                  CD: 1 track: 1   min: 2 sek: 58
34 BE FE FD A6 FF BF 3C                  CD: 1 track: 1   min: 2 sek: 59
34 BE FE FC FF FF BF 3C                  CD: 1 track: 1   min: 3 sek: 0
34 BE FE FC FE FF BF 3C                  CD: 1 track: 1   min: 3 sek: 1
34 FE FF 34 FC FF BF 3C                  CD: 41 track: 0   min: CB sek: 3
34 BE FE FC FC FF BF 3C                  CD: 1 track: 1   min: 3 sek: 3
34 BE FE FC FF 3C FE FF                  CD: 1 track: 1   min: 3 sek: 0
34 F9 F3 FF 7E 79 3F 3C                  CD: 46 track: C   min: 0 sek: 81
9F 9E 1A 5F 7E FF FF FF                  CD: 21 track: E5   min: A0 sek: 81
34 FF BF FF FC FF BF 3C                  CD: 40 track: 40   min: 0 sek: 3
532C08F7 - enable MK
FD FF FC FF BF 3C 34 14                  CD: 40 track: 3   min: 0 sek: 40
14 F9 CF FF F9 FF CF 1C                  CD: 46 track: 30   min: 0 sek: 6
532C14EB - end cmd/next cd
FF F9 FF CF 1C 14 BE BE                  CD: 46 track: 0   min: 30 sek: E3
34 FF FF CF 3C FF CF 3C                  CD: 40 track: 0   min: 30 sek: C3
FF CF 3C 34 BE FD FF FC                  CD: 70 track: C3   min: CB sek: 41
34 FF CF FF F9 FF CF 3C                  CD: 40 track: 30   min: 0 sek: 6
FD FF F9 FF CF 3C 34 BE                  CD: 40 track: 6   min: 0 sek: 30
34 BE FD FF BE E7 CF 3C                  CD: 1 track: 2   min: 0 sek: 41
34 BE FD FF F8 FF CF 3C                  CD: 1 track: 2   min: 0 sek: 7
34 BE FD FF FC 7F E7 9E                  CD: 1 track: 2   min: 0 sek: 3
34 BE FD FF F8 FF CF 3C                  CD: 1 track: 2   min: 0 sek: 7
34 BE FD FF F7 FF CF 3C                  CD: 1 track: 2   min: 0 sek: 8
34 7D FB FF EF FF 9F 3C                  CD: C2 track: 4   min: 0 sek: 10
1A 5F 7E FF FB FF E7 9E                  CD: E0 track: 81   min: 0 sek: 4
34 BE FD FF F7 FF CF 3C                  CD: 1 track: 2   min: 0 sek: 8
34 5F 7E FF FB FF E7 9E                  CD: E0 track: 81   min: 0 sek: 4
34 FF CF FB F7 FF CF 3C                  CD: 40 track: 30   min: 4 sek: 8
BE FD FF F7 FF CF 3C 34                  CD: 42 track: 0   min: 8 sek: 0
34 BE FD FF 3C FD CF 3C                  CD: 1 track: 2   min: 0 sek: C3
34 BE FD FF F7 FF E7 9E                  CD: 1 track: 2   min: 0 sek: 8
1A 5F 7E FF FB FF E7 9E                  CD: E0 track: 81   min: 0 sek: 4
34 BE FD FF F7 FF CF 3C                  CD: 1 track: 2   min: 0 sek: 8
34 BE FD FF F6 FF CF 3C                  CD: 1 track: 2   min: 0 sek: 9
34 BE FD FF F6 FF CF 3E                  CD: 1 track: 2   min: 0 sek: 9
34 BE FD FF F6 FF CF 3C                  CD: 1 track: 2   min: 0 sek: 9
34 BE FD FF FB 7F E7 9E                  CD: 1 track: 2   min: 0 sek: 4
34 BE FD FF F6 FF CF 3C                  CD: 1 track: 2   min: 0 sek: 9
34 BE FD FF EF FF CF 3C                  CD: 1 track: 2   min: 0 sek: 10
34 BE FD FF EF FF E7 9E                  CD: 1 track: 2   min: 0 sek: 10
34 BE FD FF EF FF CF 3C                  CD: 1 track: 2   min: 0 sek: 10
34 BE FD FF EF FF CF 1E                  CD: 1 track: 2   min: 0 sek: 10
34 BE FD FF EF FF CF 3C                  CD: 1 track: 2   min: 0 sek: 10
34 BE FD FF EE FF CF 3C                  CD: 1 track: 2   min: 0 sek: 11
34 BE FD FF ED FF CF 3C                  CD: 1 track: 2   min: 0 sek: 12
34 BE FD FF EC FF CF 3C                  CD: 1 track: 2   min: 0 sek: 13
34 BF 7E FF F6 7F E7 9E                  CD: 0 track: 81   min: 0 sek: 9
34 BE FD FF EC FF CF 3C                  CD: 1 track: 2   min: 0 sek: 13
34 BE FC FF F6 7F E7 9E                  CD: 1 track: 3   min: 0 sek: 9
34 BE FD FF EB FF CF 3C                  CD: 1 track: 2   min: 0 sek: 14
34 BE FD FF E5 FF E7 9E                  CD: 1 track: 2   min: 0 sek: 1A
34 BE FD FF EB FF CF 3C                  CD: 1 track: 2   min: 0 sek: 14
34 BE FD FF EA FF CF 3C                  CD: 1 track: 2   min: 0 sek: 15
34 BE FD FF EA FF E7 9E                  CD: 1 track: 2   min: 0 sek: 15
34 BE FD FF EA FF CF 3C                  CD: 1 track: 2   min: 0 sek: 15
34 BF 7E FF F5 7F E7 9E                  CD: 0 track: 81   min: 0 sek: A
34 BE FD FF EA FF CF 3C                  CD: 1 track: 2   min: 0 sek: 15
34 BE FD FF E9 FF CF 3C                  CD: 1 track: 2   min: 0 sek: 16
532C609F - mix CD
14 BE FD FF E8 DF CF 1C                  CD: 1 track: 2   min: 0 sek: 17
532C14EB - end cmd/next cd
34 BE FD FF E8 DF CF 3C                  CD: 1 track: 2   min: 0 sek: 17
34 BE 7E FF F4 6F E7 9E                  CD: 1 track: 81   min: 0 sek: B
34 BE FD FF E8 DF CF 3C                  CD: 1 track: 2   min: 0 sek: 17
34 BE FD FF E7 DF CF 3C                  CD: 1 track: 2   min: 0 sek: 18
34 BE FD FF E7 DF CF 9E                  CD: 1 track: 2   min: 0 sek: 18
34 BE FD FF E7 DF CF 3C                  CD: 1 track: 2   min: 0 sek: 18
34 BE FD FF E6 DF CF 3C                  CD: 1 track: 2   min: 0 sek: 19
34 BF 7E FF F3 6F E7 9E                  CD: 0 track: 81   min: 0 sek: C
34 BE FD FF E6 DF CF 3C                  CD: 1 track: 2   min: 0 sek: 19
34 BE FD FF DF DF CF 3C                  CD: 1 track: 2   min: 0 sek: 20
69 7C FD FF DF DF CF 3C                  CD: C3 track: 2   min: 0 sek: 20
1A 5F 7E FF EF EF E7 78                  CD: E0 track: 81   min: 0 sek: 10
34 FF CF FF DF DF CF 3C                  CD: 40 track: 30   min: 0 sek: 20
FD FF DF DF CF 3C 34 BE                  CD: 40 track: 20   min: 20 sek: 30
34 FD DF 34 FF DF CF 3C                  CD: 42 track: 20   min: CB sek: 0
34 BE FD FF DF DF CF 3C                  CD: 1 track: 2   min: 0 sek: 20
34 BE FD FF DE DF CF 3C                  CD: 1 track: 2   min: 0 sek: 21
34 5F 7E FF EF 6F E7 9E                  CD: E0 track: 81   min: 0 sek: 10
34 BE FD FF DE DF CF 3C                  CD: 1 track: 2   min: 0 sek: 21
34 BE FD FF DD DF CF 3C                  CD: 1 track: 2   min: 0 sek: 22
34 BE FD FF DD DF CF 3E                  CD: 1 track: 2   min: 0 sek: 22
34 BE FD FF DC DF CF 3C                  CD: 1 track: 2   min: 0 sek: 23
3A 5F 7E FF EE 6F E7 9E                  CD: E0 track: 81   min: 0 sek: 11
34 5F 7E FF EE 6F E7 9E                  CD: E0 track: 81   min: 0 sek: 11
34 BE FD FF DC DF CF 3C                  CD: 1 track: 2   min: 0 sek: 23
34 BE FD FF DC DF CF 1E                  CD: 1 track: 2   min: 0 sek: 23
34 BE FD FF DC DF CF 3C                  CD: 1 track: 2   min: 0 sek: 23
34 BE FD FF DC DF CF 9E                  CD: 1 track: 2   min: 0 sek: 23
34 BE FD FF DC DF CF 3C                  CD: 1 track: 2   min: 0 sek: 23
34 BE FD FF ED EF E7 9E                  CD: 1 track: 2   min: 0 sek: 12
34 BE FD FF DB DF CF 3C                  CD: 1 track: 2   min: 0 sek: 24
532C08F7 - enable MK
14 BE FD FF DB FF CF 1C                  CD: 1 track: 2   min: 0 sek: 24
14 7D FB FF DB FF CF 1E                  CD: C2 track: 4   min: 0 sek: 24
532C14EB - end cmd/next cd
A 5F 7E FF ED FF E7 8E                  CD: E0 track: 81   min: 0 sek: 12
34 BE FD FF DB FF CF 3C                  CD: 1 track: 2   min: 0 sek: 24
34 BE FD FF DD FF E7 9E                  CD: 1 track: 2   min: 0 sek: 22
34 BE FD FF DB FF CF 3C                  CD: 1 track: 2   min: 0 sek: 24
34 BE FD FF DA FF CF 3C                  CD: 1 track: 2   min: 0 sek: 25
34 7E FD FF DA FF CF 3C                  CD: C1 track: 2   min: 0 sek: 25
1A BE FD FF DA FF CF 3E                  CD: 1 track: 2   min: 0 sek: 25
1A 5F 7E FF ED 7F E7 9E                  CD: E0 track: 81   min: 0 sek: 12
34 BE FD FF DA FF CF 3C                  CD: 1 track: 2   min: 0 sek: 25
34 BE FD FF D9 FF CF 3C                  CD: 1 track: 2   min: 0 sek: 26
1A 5F 7E FF EC FF E7 9E                  CD: E0 track: 81   min: 0 sek: 13
34 BE FD FF D9 FF CF 3C                  CD: 1 track: 2   min: 0 sek: 26
34 BE FD FF D9 FF CF 3E                  CD: 1 track: 2   min: 0 sek: 26
34 BE FD FF D9 FF CF 3C                  CD: 1 track: 2   min: 0 sek: 26
34 BE FD FF D8 FF CF 3C                  CD: 1 track: 2   min: 0 sek: 27
34 BE FD FF D7 FF CF 3C                  CD: 1 track: 2   min: 0 sek: 28
34 BE FD FF D7 FF CF 9E                  CD: 1 track: 2   min: 0 sek: 28
34 7D FB FF AF FF 9E 3C                  CD: C2 track: 4   min: 0 sek: 50
1A 5F 7E FF EB FF E7 9E                  CD: E0 track: 81   min: 0 sek: 14
34 BE FD FF D7 FF CF 3C                  CD: 1 track: 2   min: 0 sek: 28
34 9F 7E FF EB FF E7 34                  CD: 20 track: 81   min: 0 sek: 14
34 BF CF 3C D7 FF CF 3C                  CD: 0 track: 30   min: C3 sek: 28
D7 FF CF 3C 34 BE FD FF                  CD: 40 track: 30   min: C3 sek: CB
34 FA 3C F7 D6 FF CF 3C                  CD: 45 track: C3   min: 8 sek: 29
34 BE FD FF D6 7F E7 9E                  CD: 1 track: 2   min: 0 sek: 29
34 BE FD FF D6 FF CF 3C                  CD: 1 track: 2   min: 0 sek: 29
34 BF 7E FF EB 7F E7 9E                  CD: 0 track: 81   min: 0 sek: 14
34 BE FD FF D6 FF CF 3C                  CD: 1 track: 2   min: 0 sek: 29
34 BE FD FF CF FF CF 3C                  CD: 1 track: 2   min: 0 sek: 30
34 BE FD FF CF FF CF 9E                  CD: 1 track: 2   min: 0 sek: 30
34 BE FD FF CF FF CF 3C                  CD: 1 track: 2   min: 0 sek: 30
34 BE FD FF CE FF CF 3C                  CD: 1 track: 2   min: 0 sek: 31
34 BF 7E FF E7 7F E7 9E                  CD: 0 track: 81   min: 0 sek: 18
34 BE FD FF CE FF CF 3C                  CD: 1 track: 2   min: 0 sek: 31
34 BE FE FF E7 7F E7 9E                  CD: 1 track: 1   min: 0 sek: 18
34 BE FD FF CE FF CF 3C                  CD: 1 track: 2   min: 0 sek: 31
34 BE FD FF CD FF CF 3C                  CD: 1 track: 2   min: 0 sek: 32
34 BE FD FF CD FF CF 1E                  CD: 1 track: 2   min: 0 sek: 32
34 BE FD FF CD FF CF 3C                  CD: 1 track: 2   min: 0 sek: 32
34 BE FD FF E6 FF E7 9E                  CD: 1 track: 2   min: 0 sek: 19
34 BE FD FF CD FF CF 3C                  CD: 1 track: 2   min: 0 sek: 32
34 7D FB FF 9B FF CF 3C                  CD: C2 track: 4   min: 0 sek: 64
1A 5F 7E FF E6 FF E7 9E                  CD: E0 track: 81   min: 0 sek: 19
34 BE FD FF CD FF CF 3C                  CD: 1 track: 2   min: 0 sek: 32
36 5F 7E FF E6 FF E7 9E                  CD: E0 track: 81   min: 0 sek: 19
34 BE FD FF CD FF CF 3C                  CD: 1 track: 2   min: 0 sek: 32
32 5F 7E FF E6 FF E7 9E                  CD: E0 track: 81   min: 0 sek: 19
34 BE FD FF CC FF CF 3C                  CD: 1 track: 2   min: 0 sek: 33
34 BE FD FF CC FF CF 34                  CD: 1 track: 2   min: 0 sek: 33
34 FF CF FF CC FF CF 3C                  CD: 40 track: 30   min: 0 sek: 33
BE FD FF CC FF CF 3C 34                  CD: 42 track: 0   min: 33 sek: 0
34 BE FF 3C FD FF CF 3C                  CD: 1 track: 0   min: C3 sek: 2
34 BE FD FF CB FF CF 3C                  CD: 1 track: 2   min: 0 sek: 34
34 BE FD FF CB FF E7 9E                  CD: 1 track: 2   min: 0 sek: 34
34 BE FD FF CB FF CF 3C                  CD: 1 track: 2   min: 0 sek: 34
34 BE FD FF CA FF CF 3C                  CD: 1 track: 2   min: 0 sek: 35
34 BE FD FF CA FF C7 9E                  CD: 1 track: 2   min: 0 sek: 35
34 BF 7E FF E5 7F E7 9E                  CD: 0 track: 81   min: 0 sek: 1A
34 BE FD FF CA FF CF 3C                  CD: 1 track: 2   min: 0 sek: 35
34 7D FB FF CA FF CF 3C                  CD: C2 track: 4   min: 0 sek: 35
1A 5F 7E FF E5 7F E7 9E                  CD: E0 track: 81   min: 0 sek: 1A
34 BE FD FF CA FF CF 3C                  CD: 1 track: 2   min: 0 sek: 35
34 BE FD FF CA FF CF 9E                  CD: 1 track: 2   min: 0 sek: 35
1A 5F 7E FF E5 7F E7 9E                  CD: E0 track: 81   min: 0 sek: 1A
34 BE FD FF CA FF CF 3C                  CD: 1 track: 2   min: 0 sek: 35
532CA05F - scan
14 BE FC FF FF EF CF 1C                  CD: 1 track: 3   min: 0 sek: 0
14 BE FC FF FF EF AE 1C                  CD: 1 track: 3   min: 0 sek: 0
532C14EB - end cmd/next cd
34 BE FC FF FF EF AE 3C                  CD: 1 track: 3   min: 0 sek: 0
34 BE FC FF FF EF CF 3C                  CD: 1 track: 3   min: 0 sek: 0
34 BE FC FF FF EF CF 3E                  CD: 1 track: 3   min: 0 sek: 0
34 BE FC FF FF EF CF 3C                  CD: 1 track: 3   min: 0 sek: 0
34 BE FC FF FF F7 E7 9E                  CD: 1 track: 3   min: 0 sek: 0
69 7D F9 FF FF DF 9E 7C                  CD: C2 track: 6   min: 0 sek: 0
1A 5F 7E 7F FF F7 E7 9E                  CD: E0 track: 81   min: 80 sek: 0
34 BE FC FF FF EF CF 3C                  CD: 1 track: 3   min: 0 sek: 0
34 BE FC FF FE EF CF 3C                  CD: 1 track: 3   min: 0 sek: 1
3A 7D F9 FF FE F7 E7 9C                  CD: C2 track: 6   min: 0 sek: 1
D 9F 7E 7F FF 77 E7 9C                  CD: 20 track: 81   min: 80 sek: 0
D 5F 7E 7F FF 77 E7 9E                  CD: E0 track: 81   min: 80 sek: 0
1A 5F 7E 7F FF 77 E7 9E                  CD: E0 track: 81   min: 80 sek: 0
34 BE FC FF FE EF 3C FC                  CD: 1 track: 3   min: 0 sek: 1
FF FD DF 9F 1E 1A 5F 7E                  CD: 42 track: 20   min: 60 sek: E1
7F FF 77 E7 9E 1A 5F 7E                  CD: 40 track: 88   min: 18 sek: 61
FF FE 79 5F FE EF CF 3C                  CD: 41 track: 86   min: A0 sek: 1
FF FE EF CF 3C 34 BE FC                  CD: 41 track: 10   min: 30 sek: C3
34 BE FC FE 34 FF CF 3C                  CD: 1 track: 3   min: 1 sek: CB
34 BE FC FF FD EF CF 3C                  CD: 1 track: 3   min: 0 sek: 2
34 BE FC FF FD EF C7 9E                  CD: 1 track: 3   min: 0 sek: 2
34 BE FC FF FD EF CF 3C                  CD: 1 track: 3   min: 0 sek: 2
34 BE FC FF FE F7 E7 9E                  CD: 1 track: 3   min: 0 sek: 1
34 DF 7E 7F FE F7 E7 9E                  CD: 60 track: 81   min: 80 sek: 1
34 BE FC FF FD EF CF 3C                  CD: 1 track: 3   min: 0 sek: 2
34 BE FC FF FD EF CF 9E                  CD: 1 track: 3   min: 0 sek: 2
34 BE FC FF FD EF CF 3C                  CD: 1 track: 3   min: 0 sek: 2
34 BE FC FF FC EF CF 3C                  CD: 1 track: 3   min: 0 sek: 3
34 BE FC FF FE 77 E7 9E                  CD: 1 track: 3   min: 0 sek: 1
34 BE FC FF FC EF CF 3C                  CD: 1 track: 3   min: 0 sek: 3
34 BE FC FF FB EF CF 3C                  CD: 1 track: 3   min: 0 sek: 4
34 7D FC FF FB EF CF 3C                  CD: C2 track: 3   min: 0 sek: 4
1A 5F 7E 7F FD F7 E7 9E                  CD: E0 track: 81   min: 80 sek: 2
34 BE FC FF FA EF CF 3C                  CD: 1 track: 3   min: 0 sek: 5
34 7D F9 FF F5 DF CF 3C                  CD: C2 track: 6   min: 0 sek: A
1A 5F 7E 7F FD 77 E7 9E                  CD: E0 track: 81   min: 80 sek: 2
34 BE FC FF FA EF CF 3C                  CD: 1 track: 3   min: 0 sek: 5
34 BE FC FF FA EF E7 9E                  CD: 1 track: 3   min: 0 sek: 5
34 BE FC FF FA EF CF 3C                  CD: 1 track: 3   min: 0 sek: 5
34 BE FC FF F9 EF CF 3C                  CD: 1 track: 3   min: 0 sek: 6
34 BE FC 7F FC F7 E7 9E                  CD: 1 track: 3   min: 80 sek: 3
34 BE FC FF F9 EF CF 3C                  CD: 1 track: 3   min: 0 sek: 6
34 BE FC FF F9 EF E7 9E                  CD: 1 track: 3   min: 0 sek: 6
34 BE FC FF F9 EF CF 3C                  CD: 1 track: 3   min: 0 sek: 6
34 BE FC FF F8 EF CF 3C                  CD: 1 track: 3   min: 0 sek: 7
34 BE FC FF F8 77 E7 9E                  CD: 1 track: 3   min: 0 sek: 7
34 BE FC FF F8 EF CF 3C                  CD: 1 track: 3   min: 0 sek: 7
34 5F 7E 7F FC 77 E7 9E                  CD: E0 track: 81   min: 80 sek: 3
34 BE FC FF F8 EF CF 3C                  CD: 1 track: 3   min: 0 sek: 7
34 BE FC FF F7 EF CF 3C                  CD: 1 track: 3   min: 0 sek: 8
34 BE FC FF FB F7 E7 9E                  CD: 1 track: 3   min: 0 sek: 4
34 BE FC FF F7 EF CF 3C                  CD: 1 track: 3   min: 0 sek: 8
34 BE FC FF F6 EF CF 3C                  CD: 1 track: 3   min: 0 sek: 9
34 BF 7E 7F FB 77 E7 9E                  CD: 0 track: 81   min: 80 sek: 4
34 BE FC FF F6 EF CF 3C                  CD: 1 track: 3   min: 0 sek: 9
34 7D F9 FF ED DF 9F 3C                  CD: C2 track: 6   min: 0 sek: 12
1A BE FC FF F7 77 E7 9E                  CD: 1 track: 3   min: 0 sek: 8
1A BE FC FF F6 EF CF 9E                  CD: 1 track: 3   min: 0 sek: 9
1A 5F 7E 7F F7 F7 E7 9E                  CD: E0 track: 81   min: 80 sek: 8
34 BE FC FF EF EF CF 3C                  CD: 1 track: 3   min: 0 sek: 10
9F 7E 7F F7 F7 E7 9E 1A                  CD: C1 track: 80   min: 8 sek: 8
BE FC FF EF EF CF 3C 34                  CD: 43 track: 0   min: 10 sek: 10
BF 7E 7F F7 E7 BE EF 3C                  CD: C1 track: 80   min: 8 sek: 18
BE FC FF EF EF CF 3C 34                  CD: 43 track: 0   min: 10 sek: 10
34 BE FC FF EF 79 FC EF                  CD: 1 track: 3   min: 0 sek: 10
CF 3C 34 BE FC FF EF EF                  CD: 83 track: CB   min: 41 sek: 3
CF 9E 1A 5F 7E 7F F7 F7                  CD: 21 track: E5   min: A0 sek: 81
CF 3C 34 BE FC FF EF EF                  CD: 83 track: CB   min: 41 sek: 3
CF 3C 34 BE FB FF FF EF                  CD: 83 track: CB   min: 41 sek: 4
AE 3C 36 5F 7D FF FF F7                  CD: 83 track: C9   min: A0 sek: 82
AE 3C 34 BE FB FF FF 3C                  CD: 83 track: CB   min: 41 sek: 4
34 BE FB FF FF EF AE 3C                  CD: 1 track: 4   min: 0 sek: 0
34 BE 7D FF FF F7 D7 1E                  CD: 1 track: 82   min: 0 sek: 0
34 BE FB FF FF EF CF 3C                  CD: 1 track: 4   min: 0 sek: 0
34 BF 7D FF FF F7 E7 9E                  CD: 0 track: 82   min: 0 sek: 0
34 BE FB FF FF EF CF 3C                  CD: 1 track: 4   min: 0 sek: 0
34 BE FB FF FE EF CF 3C                  CD: 1 track: 4   min: 0 sek: 1
34 BE FB FF FD EF CF 3C                  CD: 1 track: 4   min: 0 sek: 2
34 5F 7D FF FE F7 E7 9E                  CD: E0 track: 82   min: 0 sek: 1
34 BE FB FF FD EF CF 3C                  CD: 1 track: 4   min: 0 sek: 2
3A 5F 7D FF FE F7 E7 9E                  CD: E0 track: 82   min: 0 sek: 1
34 BE FB FF FD EF CF 3C                  CD: 1 track: 4   min: 0 sek: 2
34 BE FB FF FC EF CF 3C                  CD: 1 track: 4   min: 0 sek: 3
34 BE FB FF FE 77 E7 9E                  CD: 1 track: 4   min: 0 sek: 1
34 BE FB FF FC EF CF 3C                  CD: 1 track: 4   min: 0 sek: 3
34 BE FB FF FC EF E7 9E                  CD: 1 track: 4   min: 0 sek: 3
34 BE FB FF FC EF CF 3C                  CD: 1 track: 4   min: 0 sek: 3
532C38C7 - seekforward MK
94 2C E8 8E 98 CE FF 9C                  CD: 93 track: 17   min: 71 sek: 67
94 BC FE FF FF FF 6F 9C                  CD: 3 track: 1   min: 0 sek: 0
532C14EB - end cmd/next cd
94 2B E6 6E 87 D7 FF 9C                  CD: 94 track: 19   min: 91 sek: 78
B4 BC FE FF FF FF 6F BC                  CD: 3 track: 1   min: 0 sek: 0
B4 35 75 57 7F BC FF BC                  CD: 8A track: 8A   min: A8 sek: 80
B4 BC FE FF FF FF 6F BC                  CD: 3 track: 1   min: 0 sek: 0
B4 2E EC CE AD DC FF BC                  CD: 91 track: 13   min: 31 sek: 52
B4 BC FE FF FF FF 6F BC                  CD: 3 track: 1   min: 0 sek: 0
B4 6D 0 FF FF FF FF BC                  CD: D2 track: FF   min: 0 sek: 0
B4 FE FF 2C 8E CE FF BC                  CD: 41 track: 0   min: D3 sek: 71
B4 2C E8 8E 98 CE FF BC                  CD: 93 track: 17   min: 71 sek: 67
B4 2B E6 6E FF E7 FF BC                  CD: 94 track: 19   min: 91 sek: 0
B4 BC FE FF FF FF 6F BC                  CD: 3 track: 1   min: 0 sek: 0
B4 29 E8 8E 86 67 FF DE                  CD: 96 track: 17   min: 71 sek: 79
B4 BC FE FF FF FF 6F BC                  CD: 3 track: 1   min: 0 sek: 0
B4 2E EC CC AD DC FF BC                  CD: 91 track: 13   min: 33 sek: 52
B4 FF BC 0 FF FF FF BC                  CD: 40 track: 43   min: FF sek: 0
B4 6D 0 FF FF FF FF BC                  CD: D2 track: FF   min: 0 sek: 0
B4 2C E8 98 FF BC FF BC                  CD: 93 track: 17   min: 67 sek: 0
B4 BC FE FF FF FF 6F BC                  CD: 3 track: 1   min: 0 sek: 0
B4 BC FE FF FF FF DE EA                  CD: 3 track: 1   min: 0 sek: 0
B4 AE FF FF FF FF 6F B8                  CD: 11 track: 0   min: 0 sek: 0
FF FF FF 6F B8 B4 2C F4                  CD: 40 track: 0   min: 90 sek: 47
B4 BC FF FB B4 AD FF BC                  CD: 3 track: 0   min: 4 sek: 4B
B4 2E EC CE AD DC FF BC                  CD: 91 track: 13   min: 31 sek: 52
B4 6D 0 FF FF FF FE FF                  CD: D2 track: FF   min: 0 sek: 0
B4 BC FE FF FF FF 6F BC                  CD: 3 track: 1   min: 0 sek: 0
B4 2B E6 6E 87 D7 FF BC                  CD: 94 track: 19   min: 91 sek: 78
B4 BC FE FF FF FF B7 DE                  CD: 3 track: 1   min: 0 sek: 0
B2 15 75 57 4D 6D 7F DE                  CD: AA track: 8A   min: A8 sek: B2
B4 BC FE FF B4 86 FF BC                  CD: 3 track: 1   min: 0 sek: 4B
B4 29 E8 8E 86 CF FF BC                  CD: 96 track: 17   min: 71 sek: 79
B4 2E EC CE AD BC FE FF                  CD: 91 track: 13   min: 31 sek: 52
B4 FE FF FF FF 6F BC BC                  CD: 41 track: 0   min: 0 sek: 0
BC B4 BC FE FF FF FF 2C                  CD: B track: 43   min: 1 sek: 0
B4 8E EF FE FF FF 6F BC                  CD: 31 track: 10   min: 1 sek: 0
BC FE FF FF FF 6F BC B4                  CD: 41 track: 0   min: 0 sek: 0
B4 BC FE FF BC EA FF BC                  CD: 3 track: 1   min: 0 sek: 43
B4 2A EA AE 9A DA FF BC                  CD: 95 track: 15   min: 51 sek: 65
B4 29 E8 8E 86 2D FF 6F                  CD: 96 track: 17   min: 71 sek: 79
B4 BC FE FF FF FF 6F BC                  CD: 3 track: 1   min: 0 sek: 0
B4 6D 0 FF FF FF FF BC                  CD: D2 track: FF   min: 0 sek: 0
B4 BC FE FF FF FF 6F BC                  CD: 3 track: 1   min: 0 sek: 0
B4 2C E8 8E 98 CE FF BC                  CD: 93 track: 17   min: 71 sek: 67
B4 BC FE FF B4 87 FF BC                  CD: 3 track: 1   min: 0 sek: 4B
B4 2B E6 6E 87 D7 FF BC                  CD: 94 track: 19   min: 91 sek: 78
B4 2A EA AE 9A FF 2F FF                  CD: 95 track: 15   min: 51 sek: 65
B4 BC FE FF FF FF EF BC                  CD: 3 track: 1   min: 0 sek: 0
B4 BC FE FF FF FF F7 DE                  CD: 3 track: 1   min: 0 sek: 0
B4 9C DC BC FF FF F7 9E                  CD: 23 track: 23   min: 43 sek: 0
36 5E 7F 7F FF FF F7 9E                  CD: E1 track: 80   min: 80 sek: 0
34 BC FC FF 3C E8 CE 3C                  CD: 3 track: 3   min: 0 sek: C3
34 2C E8 8E 98 CE FF 3C                  CD: 93 track: 17   min: 71 sek: 67
34 2B E6 6E 87 D7 1A FF                  CD: 94 track: 19   min: 91 sek: 78
532C7887 - down
34 BC FE FF FF FF EF 3C                  CD: 3 track: 1   min: 0 sek: 0
532C14EB - end cmd/next cd
14 BC FF 34 8E CF FF 3C                  CD: 3 track: 0   min: CB sek: 71
34 29 E8 8E 86 CF FF 3C                  CD: 96 track: 17   min: 71 sek: 79
34 2E EC CE FF BC FF 3C                  CD: 91 track: 13   min: 31 sek: 0
34 BC E8 FF FF FF EF 3C                  CD: 3 track: 17   min: 0 sek: 0
34 2C E8 8E 98 CE FF 3C                  CD: 93 track: 17   min: 71 sek: 67
34 BC E8 FF FF FF EF 3C                  CD: 3 track: 17   min: 0 sek: 0
34 2B E6 6E 87 D7 FF 3C                  CD: 94 track: 19   min: 91 sek: 78
34 E8 FF 2A 9A DA FF 3E                  CD: 57 track: 0   min: D5 sek: 65
34 2A EA AE 9A DA FF 3E                  CD: 95 track: 15   min: 51 sek: 65
34 29 43 FF BC FF EF 3C                  CD: 96 track: BC   min: 0 sek: 43
34 BC E8 FF FF FF EF 3C                  CD: 3 track: 17   min: 0 sek: 0
34 6D 0 FF FF FF FF 3C                  CD: D2 track: FF   min: 0 sek: 0
34 BC E8 FF FF FF EF 3C                  CD: 3 track: 17   min: 0 sek: 0
34 2C E8 8E 98 CE FF 3C                  CD: 93 track: 17   min: 71 sek: 67
34 7F FF 6E 87 D7 FF 3C                  CD: C0 track: 0   min: 91 sek: 78
E6 6E 87 D7 FF 3C 34 BC                  CD: D1 track: 78   min: 28 sek: 0
34 2A AE 3C BC FF EF 3C                  CD: 95 track: 51   min: C3 sek: 43
34 BC E8 FF FF FF EF 3C                  CD: 3 track: 17   min: 0 sek: 0
34 2E EC CE AD DC FF 3C                  CD: 91 track: 13   min: 31 sek: 52
34 BC E8 FF FF FF EF 3C                  CD: 3 track: 17   min: 0 sek: 0
34 6D 0 FF FF FF FF D2                  CD: D2 track: FF   min: 0 sek: 0
34 FF E7 8E 98 CE FF 3C                  CD: 40 track: 18   min: 71 sek: 67
E8 8E 98 CE FF 3C 34 BC                  CD: 31 track: 67   min: 31 sek: 0
34 6E 3C BC FF FF EF 3C                  CD: D1 track: C3   min: 43 sek: 0
34 BC E8 FF FF FF EF 3C                  CD: 3 track: 17   min: 0 sek: 0
34 29 E8 8E 86 CF FF 3C                  CD: 96 track: 17   min: 71 sek: 79
34 BC E8 FF FF FF AE 3C                  CD: 3 track: 17   min: 0 sek: 0
34 2C E8 8E 98 CE 34 FF                  CD: 93 track: 17   min: 71 sek: 67
34 E8 FF FF FF AE 3C 3C                  CD: 57 track: 0   min: 0 sek: 0
532C7887 - down
3C 34 BC E8 FF FF E8 CE                  CD: 8B track: 43   min: 17 sek: 0
14 E8 8E 98 CE FF 1C 1C                  CD: 57 track: 71   min: 67 sek: 31
532C14EB - end cmd/next cd
1C 14 2C 8E FF BC FF 3C                  CD: AB track: D3   min: 71 sek: 0
34 BC E9 FF FF FF AE 3C                  CD: 3 track: 16   min: 0 sek: 0
34 BC E9 FF FF FF D7 1E                  CD: 3 track: 16   min: 0 sek: 0
34 BC E9 FF FF FF AE 3C                  CD: 3 track: 16   min: 0 sek: 0
34 BC E9 FF FF FF AE 3E                  CD: 3 track: 16   min: 0 sek: 0
34 BC E9 FF FF FF AE 3C                  CD: 3 track: 16   min: 0 sek: 0
34 5E 74 FF FF FF D7 1E                  CD: E1 track: 8B   min: 0 sek: 0
34 BC E9 FF FF FF AE 3C                  CD: 3 track: 16   min: 0 sek: 0
34 BC E9 FF FF FF D7 1E                  CD: 3 track: 16   min: 0 sek: 0
34 BC E9 FF FF FF AE 3C                  CD: 3 track: 16   min: 0 sek: 0
34 BC E9 FF FF FF AE 3E                  CD: 3 track: 16   min: 0 sek: 0
34 BC E9 FF FF FF AE 3C                  CD: 3 track: 16   min: 0 sek: 0
34 BC E9 FF FF FF CF 3C                  CD: 3 track: 16   min: 0 sek: 0
34 BC E8 FF FF FF E7 9E                  CD: 3 track: 17   min: 0 sek: 0
34 BC E9 FF FF FF CF 3C                  CD: 3 track: 16   min: 0 sek: 0
532C7887 - down
14 BC EA FF FF FF AE 1C                  CD: 3 track: 15   min: 0 sek: 0
532C14EB - end cmd/next cd
34 BC EA FF FF FF AE 3C                  CD: 3 track: 15   min: 0 sek: 0
34 BC EA FF FF FF CF 3C                  CD: 3 track: 15   min: 0 sek: 0
532C08F7 - enable MK
14 BC E9 FF FF FF CF 1C                  CD: 3 track: 16   min: 0 sek: 0
14 BC E9 FF FF FF AE 1C                  CD: 3 track: 16   min: 0 sek: 0
532C14EB - end cmd/next cd
34 BC E9 FF FF FF AE 3C                  CD: 3 track: 16   min: 0 sek: 0
34 BC E9 FF FF FF CF 3C                  CD: 3 track: 16   min: 0 sek: 0
34 BC E9 FF FF FF E7 9E                  CD: 3 track: 16   min: 0 sek: 0
34 BC E9 FF FF FF CF 3C                  CD: 3 track: 16   min: 0 sek: 0
34 BC E9 FF FF FF E7 9E                  CD: 3 track: 16   min: 0 sek: 0
34 BC E9 FF FF FF CF 3C                  CD: 3 track: 16   min: 0 sek: 0
34 BC E9 FF FE FF CF 3C                  CD: 3 track: 16   min: 0 sek: 1
532C7887 - down
14 BE 74 FF FF FF E7 8E                  CD: 1 track: 8B   min: 0 sek: 0
14 BC E9 FF FF FF AE 1C                  CD: 3 track: 16   min: 0 sek: 0
532C14EB - end cmd/next cd
34 BC E9 FF FF FF AE 3C                  CD: 3 track: 16   min: 0 sek: 0
34 BC E9 FF FF FF CF 3C                  CD: 3 track: 16   min: 0 sek: 0
3A 5E 74 FF FF FF E7 9E                  CD: E1 track: 8B   min: 0 sek: 0
34 BC E9 FF FF FF CF 3C                  CD: 3 track: 16   min: 0 sek: 0
34 BC EC FF FF FF E7 9E                  CD: 3 track: 13   min: 0 sek: 0
34 BC E9 FF FF FF CF 3C                  CD: 3 track: 16   min: 0 sek: 0
34 BC E9 FF FE FF CF 3C                  CD: 3 track: 16   min: 0 sek: 1
532C7887 - down
14 BC E9 FF FF FF AE 1C                  CD: 3 track: 16   min: 0 sek: 0
532C14EB - end cmd/next cd
14 BC E9 FF FF FF B7 E                  CD: 3 track: 16   min: 0 sek: 0
32 5E 74 FF FF FF D7 1E                  CD: E1 track: 8B   min: 0 sek: 0
34 BC E9 FF FF FF AE 3C                  CD: 3 track: 16   min: 0 sek: 0
34 BC E9 FF FF 3C FF CF                  CD: 3 track: 16   min: 0 sek: 0
3C 34 BC E9 FF FF FF CF                  CD: 8B track: 43   min: 16 sek: 0
3C 34 BC E9 FF FF FF E7                  CD: 8B track: 43   min: 16 sek: 0
3C 34 BC E9 FF FF FF CF                  CD: 8B track: 43   min: 16 sek: 0
532C7887 - down
3C 14 BC EA FF FF FF CF                  CD: AB track: 43   min: 15 sek: 0
1C 14 BC EA FF FF FF AE                  CD: AB track: 43   min: 15 sek: 0
532C14EB - end cmd/next cd
1C 34 5E 75 7F FF FF D7                  CD: 8B track: A1   min: 8A sek: 80
532C7887 - down
3C 34 BC EA FF FF FF AE                  CD: 8B track: 43   min: 15 sek: 0
14 BC EB FF FF FF AE 1C                  CD: 3 track: 14   min: 0 sek: 0
532C14EB - end cmd/next cd
34 BC EB FF FF FF AE 3C                  CD: 3 track: 14   min: 0 sek: 0
34 BC EB FF FF FF CF 3C                  CD: 3 track: 14   min: 0 sek: 0
34 BC EB FF FF FF E7 9E                  CD: 3 track: 14   min: 0 sek: 0
34 BC EB FF FF FF CF 3C                  CD: 3 track: 14   min: 0 sek: 0
34 BC ED FF FF FF E7 9E                  CD: 3 track: 12   min: 0 sek: 0
34 BC EB FF FF FF CF 3C                  CD: 3 track: 14   min: 0 sek: 0
34 BC EB FF FF FF CF 1E                  CD: 3 track: 14   min: 0 sek: 0
34 BC EB FF FF FF CF 3C                  CD: 3 track: 14   min: 0 sek: 0
532C7887 - down
14 BC EC FF FF FF CF 1C                  CD: 3 track: 13   min: 0 sek: 0
14 BC EC FF FF FF AE 1C                  CD: 3 track: 13   min: 0 sek: 0
532C14EB - end cmd/next cd
34 BC EC FF FF FF AE 3C                  CD: 3 track: 13   min: 0 sek: 0
532C7887 - down
14 BC ED FF FF FF AE 1C                  CD: 3 track: 12   min: 0 sek: 0
532C14EB - end cmd/next cd
34 BC ED FF FF FF AE 3C                  CD: 3 track: 12   min: 0 sek: 0
34 BC EC FF FF FF D7 1E                  CD: 3 track: 13   min: 0 sek: 0
34 BC ED FF FF FF AE 3C                  CD: 3 track: 12   min: 0 sek: 0
34 BC ED FF FF FF D7 1E                  CD: 3 track: 12   min: 0 sek: 0
34 BC ED FF FF FF AE 3C                  CD: 3 track: 12   min: 0 sek: 0
34 5E 76 FF FF FF D7 1E                  CD: E1 track: 89   min: 0 sek: 0
34 BC ED FF FF FF AE 3C                  CD: 3 track: 12   min: 0 sek: 0
34 BC EE FF FF FF D7 1E                  CD: 3 track: 11   min: 0 sek: 0
34 BC ED FF FF FF AE 3C                  CD: 3 track: 12   min: 0 sek: 0
34 BC ED FF FF FF AE 3E                  CD: 3 track: 12   min: 0 sek: 0
34 BC ED FF FF FF AE 3C                  CD: 3 track: 12   min: 0 sek: 0
34 79 DB FF FF FF 5C 7C                  CD: C6 track: 24   min: 0 sek: 0
1A 5E 76 FF FF FF D7 1E                  CD: E1 track: 89   min: 0 sek: 0
34 BC ED FF FF FF AE 3C                  CD: 3 track: 12   min: 0 sek: 0
34 BC ED FF FF FF AE 3E                  CD: 3 track: 12   min: 0 sek: 0
34 BC ED FF FF FF AE 3C                  CD: 3 track: 12   min: 0 sek: 0
34 79 DB FF FF FF 5C 3C                  CD: C6 track: 24   min: 0 sek: 0
D 5E 76 FF FF FF D7 1E                  CD: E1 track: 89   min: 0 sek: 0
34 BC ED FF FF FF AE 3C                  CD: 3 track: 12   min: 0 sek: 0
34 BC ED FF FF FF AE 3C                  CD: 3 track: 12   min: 0 sek: 0
532C08F7 - enable MK
14 BC EC FF FF FF AE 1C                  CD: 3 track: 13   min: 0 sek: 0
532C14EB - end cmd/next cd
34 BC EC FF FF FF AE 3C                  CD: 3 track: 13   min: 0 sek: 0
532C7887 - down
14 BC ED FF FF FF AE 1C                  CD: 3 track: 12   min: 0 sek: 0
532C14EB - end cmd/next cd
14 5E 76 FF FF FF D7 E                  CD: E1 track: 89   min: 0 sek: 0
34 BC ED FF FF FF AE 3C                  CD: 3 track: 12   min: 0 sek: 0
532C7887 - down
34 BC ED FF FF FF AF 1E                  CD: 3 track: 12   min: 0 sek: 0
14 BC EE FF FF FF AE 1C                  CD: 3 track: 11   min: 0 sek: 0
532C14EB - end cmd/next cd
34 BC EE FF FF FF AE 3C                  CD: 3 track: 11   min: 0 sek: 0
34 BC EE FF FF FF CF 3C                  CD: 3 track: 11   min: 0 sek: 0
34 BC EE FF FF FF E7 9E                  CD: 3 track: 11   min: 0 sek: 0
34 BC EE FF FF FF CF 3C                  CD: 3 track: 11   min: 0 sek: 0
69 79 DD FF FF FF CF 3C                  CD: C6 track: 22   min: 0 sek: 0
1A 5E 77 7F FF FF E7 9E                  CD: E1 track: 88   min: 80 sek: 0
34 BE 77 7F FF FF E7 9E                  CD: 1 track: 88   min: 80 sek: 0
34 BC EE FF FF FF CF 3C                  CD: 3 track: 11   min: 0 sek: 0
69 79 DD FF FF FF CF 3C                  CD: C6 track: 22   min: 0 sek: 0
1A BC EE FF FF FF CF 3C                  CD: 3 track: 11   min: 0 sek: 0
34 BC EE FF FE FF CF 3C                  CD: 3 track: 11   min: 0 sek: 1
34 BC EE FF FE 7F E7 9E                  CD: 3 track: 11   min: 0 sek: 1
34 BC EE FF FE FF CF 3C                  CD: 3 track: 11   min: 0 sek: 1
34 BC EE FF FD FF CF 3C                  CD: 3 track: 11   min: 0 sek: 2
69 79 DE FF FD FF CF 3C                  CD: C6 track: 21   min: 0 sek: 2
1A 5E 77 7F FE FF E7 9E                  CD: E1 track: 88   min: 80 sek: 1
34 BC EE FF FD FF CF 3C                  CD: 3 track: 11   min: 0 sek: 2
34 BC EE FF FD FF E7 9E                  CD: 3 track: 11   min: 0 sek: 2
34 BC EE FF FD FF CF 3C                  CD: 3 track: 11   min: 0 sek: 2
34 BC EE FF FC FF CF 3C                  CD: 3 track: 11   min: 0 sek: 3
34 BC EE FF FE 7F E7 9E                  CD: 3 track: 11   min: 0 sek: 1
34 BC EE FF FC FF CF 3C                  CD: 3 track: 11   min: 0 sek: 3
34 BC EE FF FE 7F E7 9E                  CD: 3 track: 11   min: 0 sek: 1
34 BC EE FF FC FF CF 3C                  CD: 3 track: 11   min: 0 sek: 3
34 BC 77 7F FE 7F E7 9E                  CD: 3 track: 88   min: 80 sek: 1
34 BC EE FF FC FF CF 3C                  CD: 3 track: 11   min: 0 sek: 3
34 BC EE FF FE 7F E7 9E                  CD: 3 track: 11   min: 0 sek: 1
34 BC EE FF FC FF CF 3C                  CD: 3 track: 11   min: 0 sek: 3
34 BC EE FF FB FF CF 3C                  CD: 3 track: 11   min: 0 sek: 4
34 5E 77 7F FD FF E7 9E                  CD: E1 track: 88   min: 80 sek: 2
34 BC EF 7F FD FF E7 9E                  CD: 3 track: 10   min: 80 sek: 2
34 BC EE FF FB FF CF 3C                  CD: 3 track: 11   min: 0 sek: 4
34 BC EE FF FD FF E7 9E                  CD: 3 track: 11   min: 0 sek: 2
34 BC EE FF FB FF CF BC                  CD: 3 track: 11   min: 0 sek: 4
EE FF FB FF CF 3C 34 BC                  CD: 40 track: 4   min: 0 sek: 30
EE FF FB FF CF 3C 3A 5E                  CD: 40 track: 4   min: 0 sek: 30
EE FF FB FF CF 3C 34 BC                  CD: 40 track: 4   min: 0 sek: 30
EE FF FA FF CF 3C 34 BC                  CD: 40 track: 5   min: 0 sek: 30
EE FF F9 FF CF 3C 34 BC                  CD: 40 track: 6   min: 0 sek: 30
EE FF F8 FF CF 3C 34 BC                  CD: 40 track: 7   min: 0 sek: 30
EE FF F8 FF CF 9E 1A 5E                  CD: 40 track: 7   min: 0 sek: 30
EE FF F8 FF CF 3C 34 BC                  CD: 40 track: 7   min: 0 sek: 30
FF F8 FF CF 3C 34 BC EE                  CD: 47 track: 0   min: 30 sek: C3
FF F7 FF CF 3C 34 BC EE                  CD: 48 track: 0   min: 30 sek: C3
FF F6 FF CF 3C 34 BC EE                  CD: 49 track: 0   min: 30 sek: C3
FF F7 FF E7 9E 1A 5E 77                  CD: 48 track: 0   min: 18 sek: 61
FF EF FF CF 3C 34 BC EE                  CD: 50 track: 0   min: 30 sek: C3
FF DF FF 9E 78 6C BC 76                  CD: 60 track: 0   min: 61 sek: 87
7F F7 FF E7 9E 1A 5E 77                  CD: 48 track: 0   min: 18 sek: 61
FF EF FF CF 3C 1A 77 FF                  CD: 50 track: 0   min: 30 sek: C3
FF EF FF CF 3C 34 BC EE                  CD: 50 track: 0   min: 30 sek: C3
34 BC EE FF EF FF CF BC                  CD: 3 track: 11   min: 0 sek: 10
FF EF FF CF 3C 34 BC EE                  CD: 50 track: 0   min: 30 sek: C3
FF EF FF CF 3C 34 DE 77                  CD: 50 track: 0   min: 30 sek: C3
FF EF FF BC FF FF CF 3C                  CD: 50 track: 0   min: 43 sek: 0
FF EE FF CF 3C 34 BC EE                  CD: 51 track: 0   min: 30 sek: C3
34 BC EE FF CF BC EE 3C                  CD: 3 track: 11   min: 0 sek: 30
34 BC EE FF EE FF CF 1E                  CD: 3 track: 11   min: 0 sek: 11
34 BC EE FF EE FF CF 3C                  CD: 3 track: 11   min: 0 sek: 11
34 BC EE FF EE FF CF 9E                  CD: 3 track: 11   min: 0 sek: 11
34 DE 77 7F F7 7F E7 9E                  CD: 61 track: 88   min: 80 sek: 8
34 BC EE FF EE FF CF 3C                  CD: 3 track: 11   min: 0 sek: 11
1A BC EE 7F F7 7F E7 9E                  CD: 3 track: 11   min: 80 sek: 8
1A 5E 77 7F F7 7F E7 9E                  CD: E1 track: 88   min: 80 sek: 8
34 BC EE FF EE FF E7 9E                  CD: 3 track: 11   min: 0 sek: 11
34 BC EE FF EE FF CF 3C                  CD: 3 track: 11   min: 0 sek: 11
34 BC F7 7F F7 7F E7 9E                  CD: 3 track: 8   min: 80 sek: 8
34 BC EE FF EE FF CF 3C                  CD: 3 track: 11   min: 0 sek: 11
34 BC EE FF EE FF E7 9E                  CD: 3 track: 11   min: 0 sek: 11
34 BC EE FF EE FF CF 3C                  CD: 3 track: 11   min: 0 sek: 11
34 BC EE FF F7 7F E7 9E                  CD: 3 track: 11   min: 0 sek: 8
34 BC EE FF EE FF CF 3C                  CD: 3 track: 11   min: 0 sek: 11
34 BC 77 7F F7 7F E7 9E                  CD: 3 track: 88   min: 80 sek: 8
34 BC EE FF EE FF CF 3C                  CD: 3 track: 11   min: 0 sek: 11
34 BC EE FF ED FF CF 3C                  CD: 3 track: 11   min: 0 sek: 12
36 5E 77 7F F6 FF E7 9E                  CD: E1 track: 88   min: 80 sek: 9
34 BC EE FF ED FF CF 3C                  CD: 3 track: 11   min: 0 sek: 12
34 BC E7 7F F6 FF E7 9E                  CD: 3 track: 18   min: 80 sek: 9
34 BC EE FF ED FF CF 3C                  CD: 3 track: 11   min: 0 sek: 12
34 BC EE FF EC FF CF 3C                  CD: 3 track: 11   min: 0 sek: 13
34 BE 77 7F F6 7F E7 9E                  CD: 1 track: 88   min: 80 sek: 9
34 BC EE FF EC FF CF 3C                  CD: 3 track: 11   min: 0 sek: 13
34 BC 77 7F F6 7F E7 9E                  CD: 3 track: 88   min: 80 sek: 9
34 BC EE FF EC FF CF 9E                  CD: 3 track: 11   min: 0 sek: 13
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
